Gloeidraad/ESP32-MUSIC-PLAYER/Hardware/V1/Doc/Images/ESP32-MUSIC-PLAYER-V1-BOT.png

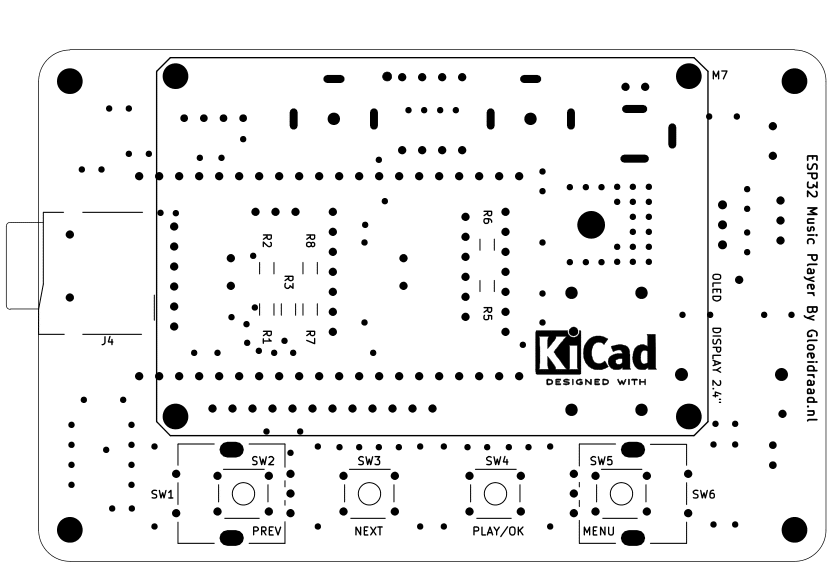
Hardware/V1/Doc/Images/ESP32-MUSIC-PLAYER-V1-BOT.png
