Gloeidraad/ESP32-MUSIC-PLAYER/Hardware/V1/Doc/Images/ESP32-MUSIC-PLAYER-V1-TOP.png

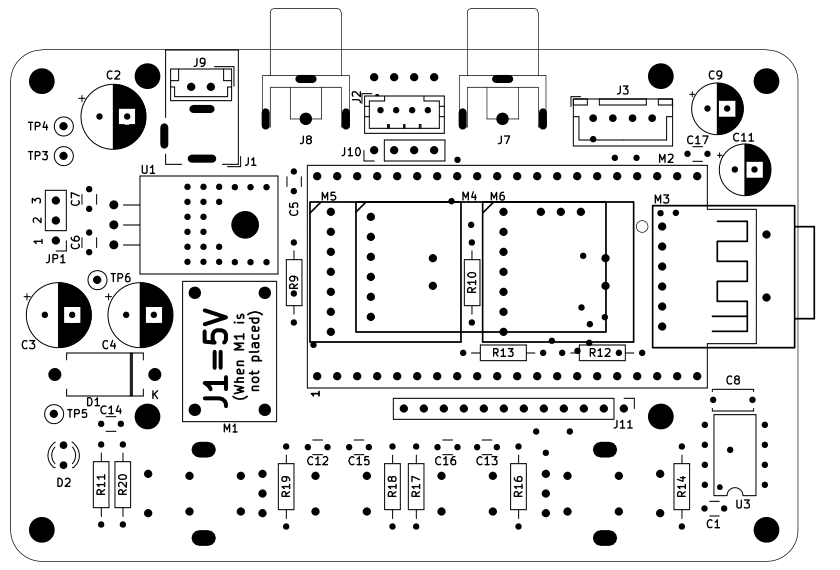
Hardware/V1/Doc/Images/ESP32-MUSIC-PLAYER-V1-TOP.png
