Gloeidraad/ESP32-MUSIC-PLAYER/Hardware/V5-SPI/ESP32-MUSIC-PLAYER-MINI-V5-PANEL/Images/assy side.png

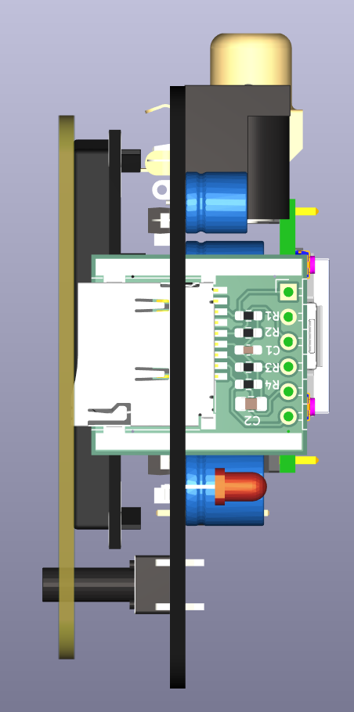
Hardware/V5-SPI/ESP32-MUSIC-PLAYER-MINI-V5-PANEL/Images/assy side.png
