Gloeidraad/ESP32-MUSIC-PLAYER/Hardware/V5-SPI/ESP32-MUSIC-PLAYER-MINI-V5-PANEL/Images/ESP23 Player in Strapubox 2515 front.jpg

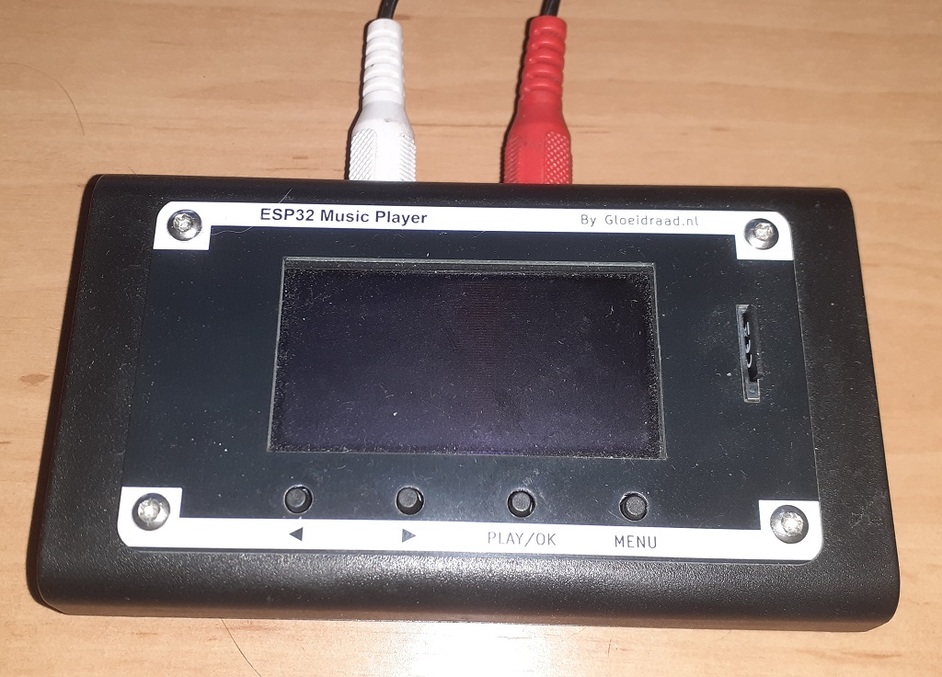
Hardware/V5-SPI/ESP32-MUSIC-PLAYER-MINI-V5-PANEL/Images/ESP23 Player in Strapubox 2515 front.jpg
