Gloeidraad/ESP32-MUSIC-PLAYER/Software/ESP32-Music-Player/src/AudioI2S/Audio.cpp

/*
 * Audio.cpp
 *
 *  Created on: Oct 26.2018
 *
 *  Version 3.0.10e
 *  Updated on: May 29.2024
 *      Author: Wolle (schreibfaul1)
 *
 */
#include "Audio.h"
#include "aac_decoder/aac_decoder.h"
#include "flac_decoder/flac_decoder.h"
#include "mp3_decoder/mp3_decoder.h"
#include "opus_decoder/opus_decoder.h"
#include "vorbis_decoder/vorbis_decoder.h"

//------------------------------------------------------------------------------------------------------------------------------------------------------------------------------------------------------
AudioBuffer::AudioBuffer(size_t maxBlockSize) {
    // if maxBlockSize isn't set use defaultspace (1600 bytes) is enough for aac and mp3 player
    if(maxBlockSize) m_resBuffSizeRAM = maxBlockSize;
    if(maxBlockSize) m_maxBlockSize = maxBlockSize;
}

AudioBuffer::~AudioBuffer() {
    if(m_buffer) free(m_buffer);
    m_buffer = NULL;
}

void AudioBuffer::setBufsize(int ram, int psram) {
    if(ram > -1) // -1 == default / no change
        m_buffSizeRAM = ram;
    if(psram > -1) m_buffSizePSRAM = psram;
}

int32_t AudioBuffer::getBufsize() { return m_buffSize; }

size_t AudioBuffer::init() {
    if(m_buffer) free(m_buffer);
    m_buffer = NULL;
    if(psramInit() && m_buffSizePSRAM > 0) {
        // PSRAM found, AudioBuffer will be allocated in PSRAM
        m_f_psram = true;
        m_buffSize = m_buffSizePSRAM;
        m_buffer = (uint8_t*)ps_calloc(m_buffSize, sizeof(uint8_t));
        m_buffSize = m_buffSizePSRAM - m_resBuffSizePSRAM;
    }
    if(m_buffer == NULL) {
        // PSRAM not found, not configured or not enough available
        m_f_psram = false;
        m_buffer = (uint8_t*)heap_caps_calloc(m_buffSizeRAM, sizeof(uint8_t), MALLOC_CAP_DEFAULT | MALLOC_CAP_INTERNAL);
        m_buffSize = m_buffSizeRAM - m_resBuffSizeRAM;
    }
    if(!m_buffer) return 0;
    m_f_init = true;
    resetBuffer();
    return m_buffSize;
}

void AudioBuffer::changeMaxBlockSize(uint16_t mbs) {
    m_maxBlockSize = mbs;
    return;
}

uint16_t AudioBuffer::getMaxBlockSize() { return m_maxBlockSize; }

size_t AudioBuffer::freeSpace() {
    if(m_readPtr >= m_writePtr) { m_freeSpace = (m_readPtr - m_writePtr); }
    else { m_freeSpace = (m_endPtr - m_writePtr) + (m_readPtr - m_buffer); }
    if(m_f_start) m_freeSpace = m_buffSize;
    return m_freeSpace - 1;
}

size_t AudioBuffer::writeSpace() {
    if(m_readPtr >= m_writePtr) {
        m_writeSpace = (m_readPtr - m_writePtr - 1); // readPtr must not be overtaken
    }
    else {
        if(getReadPos() == 0) m_writeSpace = (m_endPtr - m_writePtr - 1);
        else m_writeSpace = (m_endPtr - m_writePtr);
    }
    if(m_f_start) m_writeSpace = m_buffSize - 1;
    return m_writeSpace;
}

size_t AudioBuffer::bufferFilled() {
    if(m_writePtr >= m_readPtr) { m_dataLength = (m_writePtr - m_readPtr); }
    else { m_dataLength = (m_endPtr - m_readPtr) + (m_writePtr - m_buffer); }
    return m_dataLength;
}

size_t AudioBuffer::getMaxAvailableBytes() {
    if(m_writePtr >= m_readPtr) { m_dataLength = (m_writePtr - m_readPtr - 1); }
    else { m_dataLength = (m_endPtr - m_readPtr); }
    return m_dataLength;
}

void AudioBuffer::bytesWritten(size_t bw) {
    m_writePtr += bw;
    if(m_writePtr == m_endPtr) { m_writePtr = m_buffer; }
    if(bw && m_f_start) m_f_start = false;
}

void AudioBuffer::bytesWasRead(size_t br) {
    m_readPtr += br;
    if(m_readPtr >= m_endPtr) {
        size_t tmp = m_readPtr - m_endPtr;
        m_readPtr = m_buffer + tmp;
    }
}

uint8_t* AudioBuffer::getWritePtr() { return m_writePtr; }

uint8_t* AudioBuffer::getReadPtr() {
    size_t len = m_endPtr - m_readPtr;
    if(len < m_maxBlockSize) {                            // be sure the last frame is completed
        memcpy(m_endPtr, m_buffer, m_maxBlockSize - len); // cpy from m_buffer to m_endPtr with len
    }
    return m_readPtr;
}

void AudioBuffer::resetBuffer() {
    m_writePtr = m_buffer;
    m_readPtr = m_buffer;
    m_endPtr = m_buffer + m_buffSize;
    m_f_start = true;
    // memset(m_buffer, 0, m_buffSize); //Clear Inputbuffer
}

uint32_t AudioBuffer::getWritePos() { return m_writePtr - m_buffer; }

uint32_t AudioBuffer::getReadPos() { return m_readPtr - m_buffer; }
//------------------------------------------------------------------------------------------------------------------------------------------------------------------------------------------------------
// clang-format off
Audio::Audio(bool internalDAC /* = false */, uint8_t channelEnabled /* = I2S_SLOT_MODE_STEREO */, uint8_t i2sPort) {

    mutex_audio = xSemaphoreCreateMutex();

#ifdef AUDIO_LOG
    m_f_Log = true;
#endif

#define __malloc_heap_psram(size) \
    heap_caps_malloc_prefer(size, 2, MALLOC_CAP_DEFAULT | MALLOC_CAP_SPIRAM, MALLOC_CAP_DEFAULT | MALLOC_CAP_INTERNAL)

    m_f_psramFound = psramInit();
    if(m_f_psramFound) m_chbufSize = 4096; else m_chbufSize = 512 + 64;
    if(m_f_psramFound) m_ibuffSize = 4096; else m_ibuffSize = 512 + 64;
    m_lastHost = (char*)__malloc_heap_psram(512);
    m_outBuff = (int16_t*)__malloc_heap_psram(m_outbuffSize);
    m_chbuf = (char*)__malloc_heap_psram(m_chbufSize);
    m_ibuff = (char*)__malloc_heap_psram(m_ibuffSize);

    if(!m_chbuf || !m_lastHost || !m_outBuff || !m_ibuff) log_e("oom");

#define AUDIO_INFO(...)                     \
    {                                       \
        sprintf(m_ibuff, __VA_ARGS__);      \
        if(audio_info) audio_info(m_ibuff); \
    }

    clientsecure.setInsecure();
    m_f_channelEnabled = channelEnabled;
    m_f_internalDAC = internalDAC;
    m_i2s_num = i2sPort;  // i2s port number

    // -------- I2S configuration -------------------------------------------------------------------------------------------
#if ESP_IDF_VERSION_MAJOR == 5
    m_i2s_chan_cfg.id            = (i2s_port_t)m_i2s_num;  // I2S_NUM_AUTO, I2S_NUM_0, I2S_NUM_1
    m_i2s_chan_cfg.role          = I2S_ROLE_MASTER;        // I2S controller master role, bclk and lrc signal will be set to output
    m_i2s_chan_cfg.dma_desc_num  = 16;                     // number of DMA buffer
    m_i2s_chan_cfg.dma_frame_num = 512;                    // I2S frame number in one DMA buffer.
    m_i2s_chan_cfg.auto_clear    = true;                   // i2s will always send zero automatically if no data to send
    i2s_new_channel(&m_i2s_chan_cfg, &m_i2s_tx_handle, NULL);

    m_i2s_std_cfg.slot_cfg                = I2S_STD_PHILIPS_SLOT_DEFAULT_CONFIG(I2S_DATA_BIT_WIDTH_16BIT, I2S_SLOT_MODE_STEREO); // Set to enable bit shift in Philips mode
    m_i2s_std_cfg.gpio_cfg.bclk           = I2S_GPIO_UNUSED;           // BCLK, Assignment in setPinout()
    m_i2s_std_cfg.gpio_cfg.din            = I2S_GPIO_UNUSED;           // not used
    m_i2s_std_cfg.gpio_cfg.dout           = I2S_GPIO_UNUSED;           // DOUT, Assignment in setPinout()
    m_i2s_std_cfg.gpio_cfg.mclk           = I2S_GPIO_UNUSED;           // MCLK, Assignment in setPinout()
    m_i2s_std_cfg.gpio_cfg.ws             = I2S_GPIO_UNUSED;           // LRC,  Assignment in setPinout()
    m_i2s_std_cfg.gpio_cfg.invert_flags.mclk_inv = false;
    m_i2s_std_cfg.gpio_cfg.invert_flags.bclk_inv = false;
    m_i2s_std_cfg.gpio_cfg.invert_flags.ws_inv   = false;
    m_i2s_std_cfg.clk_cfg.sample_rate_hz = 44100;
    m_i2s_std_cfg.clk_cfg.clk_src        = I2S_CLK_SRC_DEFAULT;        // Select PLL_F160M as the default source clock
    m_i2s_std_cfg.clk_cfg.mclk_multiple  = I2S_MCLK_MULTIPLE_128;      // mclk = sample_rate * 256
    i2s_channel_init_std_mode(m_i2s_tx_handle, &m_i2s_std_cfg);
    I2Sstart(0);
    m_sampleRate = 44100;
#else
    m_i2s_config.sample_rate          = 16000;
    m_i2s_config.bits_per_sample      = I2S_BITS_PER_SAMPLE_16BIT;
    m_i2s_config.channel_format       = I2S_CHANNEL_FMT_RIGHT_LEFT;
    m_i2s_config.intr_alloc_flags     = ESP_INTR_FLAG_LEVEL1; // interrupt priority
    m_i2s_config.dma_buf_count        = 16;
    m_i2s_config.dma_buf_len          = 512;
    m_i2s_config.use_apll             = APLL_DISABLE; // must be disabled in V2.0.1-RC1
    m_i2s_config.tx_desc_auto_clear   = true;   // new in V1.0.1
    m_i2s_config.fixed_mclk           = true;
    m_i2s_config.mclk_multiple        = I2S_MCLK_MULTIPLE_128;

    if (internalDAC)  {
        #ifdef CONFIG_IDF_TARGET_ESP32  // ESP32S3 has no DAC
        printf("internal DAC");
        m_i2s_config.mode             = (i2s_mode_t)(I2S_MODE_MASTER | I2S_MODE_TX | I2S_MODE_DAC_BUILT_IN );
        m_i2s_config.communication_format = (i2s_comm_format_t)(I2S_COMM_FORMAT_STAND_MSB); // vers >= 2.0.5
        i2s_driver_install((i2s_port_t)m_i2s_num, &m_i2s_config, 0, NULL);
        i2s_set_dac_mode((i2s_dac_mode_t)m_f_channelEnabled);
        if(m_f_channelEnabled != I2S_DAC_CHANNEL_BOTH_EN) {
            m_f_forceMono = true;
        }
        #endif
    }
    else {
        m_i2s_config.mode             = (i2s_mode_t)(I2S_MODE_MASTER | I2S_MODE_TX);
        m_i2s_config.communication_format = (i2s_comm_format_t)(I2S_COMM_FORMAT_STAND_I2S); // Arduino vers. > 2.0.0
        i2s_driver_install((i2s_port_t)m_i2s_num, &m_i2s_config, 0, NULL);
        m_f_forceMono = false;
    }
    i2s_zero_dma_buffer((i2s_port_t) m_i2s_num);

#endif // ESP_IDF_VERSION_MAJOR == 5
    for(int i = 0; i < 3; i++) {
        m_filter[i].a0 = 1;
        m_filter[i].a1 = 0;
        m_filter[i].a2 = 0;
        m_filter[i].b1 = 0;
        m_filter[i].b2 = 0;
    }
    computeLimit();  // first init, vol = 21, vol_steps = 21
    m_headerTimeout = 2500; // OMT: expansion
}
//------------------------------------------------------------------------------------------------------------------------------------------------------------------------------------------------------
Audio::~Audio() {
    // I2Sstop(m_i2s_num);
    // InBuff.~AudioBuffer(); #215 the AudioBuffer is automatically destroyed by the destructor
    setDefaults();
    if(m_playlistBuff) {
        free(m_playlistBuff);
        m_playlistBuff = NULL;
    }
#if ESP_IDF_VERSION_MAJOR == 5
    i2s_del_channel(m_i2s_tx_handle);
#else
    i2s_driver_uninstall((i2s_port_t)m_i2s_num); // #215 free I2S buffer
#endif
    if(m_chbuf)       {free(m_chbuf);        m_chbuf        = NULL;}
    if(m_lastHost)    {free(m_lastHost);     m_lastHost     = NULL;}
    if(m_outBuff)     {free(m_outBuff);      m_outBuff      = NULL; }
    if(m_ibuff)       {free(m_ibuff);        m_ibuff        = NULL;}
    if(m_lastM3U8host){free(m_lastM3U8host); m_lastM3U8host = NULL;}

    vSemaphoreDelete(mutex_audio);
}
// clang-format on
//------------------------------------------------------------------------------------------------------------------------------------------------------------------------------------------------------
void Audio::setBufsize(int rambuf_sz, int psrambuf_sz) {
    if(InBuff.isInitialized()) {
        log_e("Audio::setBufsize must not be called after audio is initialized");
        return;
    }
    InBuff.setBufsize(rambuf_sz, psrambuf_sz);
};

void Audio::initInBuff() {
    if(!InBuff.isInitialized()) {
        size_t size = InBuff.init();
        if(size > 0) { AUDIO_INFO("PSRAM %sfound, inputBufferSize: %u bytes", InBuff.havePSRAM() ? "" : "not ", size - 1); }
    }
    changeMaxBlockSize(1600); // default size mp3 or aac
}

//------------------------------------------------------------------------------------------------------------------------------------------------------------------------------------------------------
esp_err_t Audio::I2Sstart(uint8_t i2s_num) {
#if ESP_IDF_VERSION_MAJOR == 5
    return i2s_channel_enable(m_i2s_tx_handle);
#else
    // It is not necessary to call this function after i2s_driver_install() (it is started automatically),
    // however it is necessary to call it after i2s_stop()
    return i2s_start((i2s_port_t)i2s_num);
#endif
}

esp_err_t Audio::I2Sstop(uint8_t i2s_num) {
#if ESP_IDF_VERSION_MAJOR == 5
    return i2s_channel_disable(m_i2s_tx_handle);
#else
    return i2s_stop((i2s_port_t)i2s_num);
#endif
}
//------------------------------------------------------------------------------------------------------------------------------------------------------------------------------------------------------
void Audio::setDefaults() {
    stopSong();
    initInBuff(); // initialize InputBuffer if not already done
    InBuff.resetBuffer();
    MP3Decoder_FreeBuffers();
    FLACDecoder_FreeBuffers();
    AACDecoder_FreeBuffers();
    OPUSDecoder_FreeBuffers();
    VORBISDecoder_FreeBuffers();
    if(m_playlistBuff) {
        free(m_playlistBuff);
        m_playlistBuff = NULL;
    } // free if stream is not m3u8
    vector_clear_and_shrink(m_playlistURL);
    vector_clear_and_shrink(m_playlistContent);
    m_hashQueue.clear();
    m_hashQueue.shrink_to_fit(); // uint32_t vector
    client.stop();
    clientsecure.stop();
    _client = static_cast<WiFiClient*>(&client); /* default to *something* so that no NULL deref can happen */
    ts_parsePacket(0, 0, 0);                     // reset ts routine
    if(m_lastM3U8host) {
        free(m_lastM3U8host);
        m_lastM3U8host = NULL;
    }
    AUDIO_INFO("buffers freed, free Heap: %lu bytes", (long unsigned int)ESP.getFreeHeap());

    m_f_timeout = false;
    m_f_chunked = false; // Assume not chunked
    m_f_firstmetabyte = false;
    m_f_playing = false;
    m_f_ssl = false;
    m_f_metadata = false;
    m_f_tts = false;
    m_f_firstCall = true;        // InitSequence for processWebstream and processLocalFile
    m_f_firstCurTimeCall = true; // InitSequence for computeAudioTime
    m_f_firstM3U8call = true;    // InitSequence for parsePlaylist_M3U8
    m_f_running = false;
    m_f_loop = false;     // Set if audio file should loop
    m_f_unsync = false;   // set within ID3 tag but not used
    m_f_exthdr = false;   // ID3 extended header
    m_f_rtsp = false;     // RTSP (m3u8)stream
    m_f_m3u8data = false; // set again in processM3U8entries() if necessary
    m_f_continue = false;
    m_f_ts = false;
    m_f_m4aID3dataAreRead = false;

    m_streamType = ST_NONE;
    m_codec = CODEC_NONE;
    m_playlistFormat = FORMAT_NONE;
    m_datamode = AUDIO_NONE;
    m_audioCurrentTime = 0; // Reset playtimer
    m_audioFileDuration = 0;
    m_audioDataStart = 0;
    m_audioDataSize = 0;
    m_avr_bitrate = 0;     // the same as m_bitrate if CBR, median if VBR
    m_bitRate = 0;         // Bitrate still unknown
    m_bytesNotDecoded = 0; // counts all not decodable bytes
    m_chunkcount = 0;      // for chunked streams
   // byteCounter = 0;     // count received data
    m_contentlength = 0;   // If Content-Length is known, count it
    m_curSample = 0;
    m_metaint = 0;        // No metaint yet
    m_LFcount = 0;        // For end of header detection
    m_controlCounter = 0; // Status within readID3data() and readWaveHeader()
    m_channels = 2;       // assume stereo #209
    m_streamTitleHash = 0;
    m_fileSize = 0;
    m_ID3Size = 0;
    m_haveNewFilePos = 0;
}

//------------------------------------------------------------------------------------------------------------------------------------------------------------------------------------------------------
void Audio::setConnectionTimeout(uint16_t timeout_ms, uint16_t timeout_ms_ssl) {
    if(timeout_ms) m_timeout_ms = timeout_ms;
    if(timeout_ms_ssl) m_timeout_ms_ssl = timeout_ms_ssl;
}

/*
    Text to speech API provides a speech endpoint based on our TTS (text-to-speech) model.
    More info: https://platform.openai.com/docs/guides/text-to-speech/text-to-speech

    Request body:
    model (string) [Required] - One of the available TTS models: tts-1 or tts-1-hd
    input (string) [Required] - The text to generate audio for. The maximum length is 4096 characters.
    voice (string) [Required] - The voice to use when generating the audio. Supported voices are alloy, echo, fable, onyx, nova, and shimmer.
    response_format (string) [Optional] - Defaults to mp3. The format to audio in. Supported formats are mp3, opus, aac, and flac.
    speed (number) [Optional] - Defaults to 1. The speed of the generated audio. Select a value from 0.25 to 4.0. 1.0 is the default.

    Usage: audio.openai_speech(OPENAI_API_KEY, "tts-1", input, "shimmer", "mp3", "1");
*/
bool Audio::openai_speech(const String& api_key, const String& model, const String& input, const String& voice, const String& response_format, const String& speed) {
    char host[] = "api.openai.com";
    char path[] = "/v1/audio/speech";

    xSemaphoreTakeRecursive(mutex_audio, portMAX_DELAY);

    if (input == "") {
        AUDIO_INFO("input text is empty");
        stopSong();
        xSemaphoreGiveRecursive(mutex_audio);
        return false;
    }

    AUDIO_INFO("Connect to new host: \"%s\"", host);
    setDefaults();
    m_f_ssl = true;

    String input_clean = "";
    for (int i = 0; i < input.length(); i++) {
        char c = input.charAt(i);
        if (c == '\"') {
            input_clean += "\\\"";
        } else if (c == '\n') {
            input_clean += "\\n";
        } else {
            input_clean += c;
        }
    }

    String post_body = "{"
        "\"model\": \"" + model + "\"," +
        "\"input\": \"" + input_clean + "\"," +
        "\"voice\": \"" + voice + "\"," +
        "\"response_format\": \"" + response_format + "\"," +
        "\"speed\": \"" + speed + "\"" +
    "}";

    String http_request =
        "POST " + String(path) + " HTTP/1.0\r\n" // UNKNOWN ERROR CODE (0050) - crashing on HTTP/1.1 need to use HTTP/1.0
        + "Host: " + String(host) + "\r\n"
        + "Authorization: Bearer " + api_key + "\r\n"
        + "Accept-Encoding: identity;q=1,*;q=0\r\n"
        + "User-Agent: nArija/1.0\r\n"
        + "Content-Type: application/json; charset=utf-8\r\n"
        + "Content-Length: " + post_body.length() + "\r\n"
        + "Connection: keep-alive\r\n" + "\r\n"
        + post_body + "\r\n"
    ;

    bool res = true;
    int port = 443;
    _client = static_cast<WiFiClient*>(&clientsecure);

    uint32_t t = millis();
    if (m_f_Log) AUDIO_INFO("connect to %s on port %d path %s", host, port, path);
    res = _client->connect(host, port, m_timeout_ms_ssl);
    if (res) {
        uint32_t dt = millis() - t;
        strcpy(m_lastHost, host);
        AUDIO_INFO("%s has been established in %lu ms, free Heap: %lu bytes", "SSL", (long unsigned int) dt, (long unsigned int) ESP.getFreeHeap());
        m_f_running = true;
    }

    m_expectedCodec = CODEC_NONE;
    m_expectedPlsFmt = FORMAT_NONE;

    if (res) {
        _client->print(http_request);
        if (response_format == "mp3") m_expectedCodec  = CODEC_MP3;
        if (response_format == "opus") m_expectedCodec  = CODEC_OPUS;
        if (response_format == "aac") m_expectedCodec  = CODEC_AAC;
        if (response_format == "flac") m_expectedCodec  = CODEC_FLAC;
        setDatamode(HTTP_RESPONSE_HEADER);
        m_streamType = ST_WEBSTREAM;
    } else {
        AUDIO_INFO("Request %s failed!", host);
        m_lastHost[0] = 0;
    }

    xSemaphoreGiveRecursive(mutex_audio);
    return res;
}

//------------------------------------------------------------------------------------------------------------------------------------------------------------------------------------------------------
bool Audio::connecttohost(const char* host, const char* user, const char* pwd) {
    // user and pwd for authentification only, can be empty

    xSemaphoreTakeRecursive(mutex_audio, portMAX_DELAY);

    if(host == NULL) {
        AUDIO_INFO("Hostaddress is empty");
        stopSong();
        xSemaphoreGiveRecursive(mutex_audio);
        return false;
    }

    uint16_t lenHost = strlen(host);

    if(lenHost >= 512 - 10) {
        AUDIO_INFO("Hostaddress is too long");
        stopSong();
        xSemaphoreGiveRecursive(mutex_audio);
        return false;
    }

    int   idx = indexOf(host, "http");
    char* l_host = (char*)malloc(lenHost + 10);
    if(idx < 0) {
        strcpy(l_host, "http://");
        strcat(l_host, host);
    }                                      // amend "http;//" if not found
    else { strcpy(l_host, (host + idx)); } // trim left if necessary

    char* h_host = NULL; // pointer of l_host without http:// or https://
    if(startsWith(l_host, "https")) h_host = strdup(l_host + 8);
    else h_host = strdup(l_host + 7);

    // initializationsequence
    int16_t  pos_slash;     // position of "/" in hostname
    int16_t  pos_colon;     // position of ":" in hostname
    int16_t  pos_ampersand; // position of "&" in hostname
    uint16_t port = 80;     // port number

    // In the URL there may be an extension, like noisefm.ru:8000/play.m3u&t=.m3u
    pos_slash = indexOf(h_host, "/", 0);
    pos_colon = indexOf(h_host, ":", 0);
    if(isalpha(h_host[pos_colon + 1])) pos_colon = -1; // no portnumber follows
    pos_ampersand = indexOf(h_host, "&", 0);

    char* hostwoext = NULL; // "skonto.ls.lv:8002" in "skonto.ls.lv:8002/mp3"
    char* extension = NULL; // "/mp3" in "skonto.ls.lv:8002/mp3"

    if(pos_slash > 1) {
        hostwoext = (char*)malloc(pos_slash + 1);
        memcpy(hostwoext, h_host, pos_slash);
        hostwoext[pos_slash] = '\0';
        uint16_t extLen = urlencode_expected_len(h_host + pos_slash);
        extension = (char*)malloc(extLen + 20);
        memcpy(extension, h_host + pos_slash, extLen);
        urlencode(extension, extLen, true);
    }
    else { // url has no extension
        hostwoext = strdup(h_host);
        extension = strdup("/");
    }

    if((pos_colon >= 0) && ((pos_ampersand == -1) || (pos_ampersand > pos_colon))) {
        port = atoi(h_host + pos_colon + 1); // Get portnumber as integer
        hostwoext[pos_colon] = '\0';         // Host without portnumber
    }

    AUDIO_INFO("Connect to new host: \"%s\"", l_host);
    setDefaults(); // no need to stop clients if connection is established (default is true)

    if(startsWith(l_host, "https")) m_f_ssl = true;
    else m_f_ssl = false;

    // optional basic authorization
    uint16_t auth = strlen(user) + strlen(pwd);
    char     authorization[base64_encode_expected_len(auth + 1) + 1];
    authorization[0] = '\0';
    if(auth > 0) {
        char toEncode[auth + 4];
        strcpy(toEncode, user);
        strcat(toEncode, ":");
        strcat(toEncode, pwd);
        b64encode((const char*)toEncode, strlen(toEncode), authorization);
    }

    //  AUDIO_INFO("Connect to \"%s\" on port %d, extension \"%s\"", hostwoext, port, extension);

    char rqh[strlen(h_host) + strlen(authorization) + 220]; // http request header
    rqh[0] = '\0';

    strcat(rqh, "GET ");
    strcat(rqh, extension);
    strcat(rqh, " HTTP/1.1\r\n");
    strcat(rqh, "Host: ");
    strcat(rqh, hostwoext);
    strcat(rqh, "\r\n");
    strcat(rqh, "Icy-MetaData:1\r\n");
    strcat(rqh, "Icy-MetaData:2\r\n");

    if(auth > 0) {
        strcat(rqh, "Authorization: Basic ");
        strcat(rqh, authorization);
        strcat(rqh, "\r\n");
    }

    strcat(rqh, "Accept-Encoding: identity;q=1,*;q=0\r\n");
    //    strcat(rqh, "User-Agent: Mozilla/5.0\r\n"); #363
    strcat(rqh, "Connection: keep-alive\r\n\r\n");

    //    if(ESP_ARDUINO_VERSION_MAJOR == 2 && ESP_ARDUINO_VERSION_MINOR == 0 && ESP_ARDUINO_VERSION_PATCH >= 3){
    //        m_timeout_ms_ssl = UINT16_MAX;  // bug in v2.0.3 if hostwoext is a IPaddr not a name
    //        m_timeout_ms = UINT16_MAX;  // [WiFiClient.cpp:253] connect(): select returned due to timeout 250 ms for
    //        fd 48
    //    } fix in V2.0.8

    bool res = true; // no need to reconnect if connection exists

    if(m_f_ssl) {
        _client = static_cast<WiFiClient*>(&clientsecure);
        if(port == 80) port = 443;
    }
    else { _client = static_cast<WiFiClient*>(&client); }

    uint32_t t = millis();
    if(m_f_Log) AUDIO_INFO("connect to %s on port %d path %s", hostwoext, port, extension);
    res = _client->connect(hostwoext, port, m_f_ssl ? m_timeout_ms_ssl : m_timeout_ms);
    if(res) {
        uint32_t dt = millis() - t;
        strcpy(m_lastHost, l_host);
        AUDIO_INFO("%s has been established in %lu ms, free Heap: %lu bytes", m_f_ssl ? "SSL" : "Connection", (long unsigned int)dt, (long unsigned int)ESP.getFreeHeap());
        m_f_running = true;
    }

    m_expectedCodec = CODEC_NONE;
    m_expectedPlsFmt = FORMAT_NONE;

    if(res) {
    //    log_i("connecttohost(): %s", rqh);
        _client->print(rqh);
        if(endsWith(extension, ".mp3" )) m_expectedCodec  = CODEC_MP3;
        if(endsWith(extension, ".aac" )) m_expectedCodec  = CODEC_AAC;
        if(endsWith(extension, ".wav" )) m_expectedCodec  = CODEC_WAV;
        if(endsWith(extension, ".m4a" )) m_expectedCodec  = CODEC_M4A;
        if(endsWith(extension, ".ogg" )) m_expectedCodec  = CODEC_OGG;
        if(endsWith(extension, ".flac")) m_expectedCodec  = CODEC_FLAC;
        if(endsWith(extension, "-flac")) m_expectedCodec  = CODEC_FLAC;
        if(endsWith(extension, ".opus")) m_expectedCodec  = CODEC_OPUS;
        if(endsWith(extension, "/opus")) m_expectedCodec  = CODEC_OPUS;
        if(endsWith(extension, ".asx" )) m_expectedPlsFmt = FORMAT_ASX;
        if(endsWith(extension, ".m3u" )) m_expectedPlsFmt = FORMAT_M3U;
        if(endsWith(extension, ".pls" )) m_expectedPlsFmt = FORMAT_PLS;
        if(endsWith(extension, ".m3u8")) {
            m_expectedPlsFmt = FORMAT_M3U8;
            if(audio_lasthost) audio_lasthost(host);
        }
        setDatamode(HTTP_RESPONSE_HEADER); // Handle header
        m_streamType = ST_WEBSTREAM;
    }
    else {
        AUDIO_INFO("Request %s failed!", l_host);
        if(audio_showstation) audio_showstation("");
        if(audio_showstreamtitle) audio_showstreamtitle("");
        if(audio_icydescription) audio_icydescription("");
        if(audio_icyurl) audio_icyurl("");
        m_lastHost[0] = 0;
    }
    if(hostwoext) {
        free(hostwoext);
        hostwoext = NULL;
    }
    if(extension) {
        free(extension);
        extension = NULL;
    }
    if(l_host) {
        free(l_host);
        l_host = NULL;
    }
    if(h_host) {
        free(h_host);
        h_host = NULL;
    }
    xSemaphoreGiveRecursive(mutex_audio);
    return res;
}
//------------------------------------------------------------------------------------------------------------------------------------------------------------------------------------------------------
bool Audio::httpPrint(const char* host) {
    // user and pwd for authentification only, can be empty

    if(host == NULL) {
        AUDIO_INFO("Hostaddress is empty");
        stopSong();
        return false;
    }

    char* h_host = NULL; // pointer of l_host without http:// or https://

    if(startsWith(host, "https")) m_f_ssl = true;
    else m_f_ssl = false;

    if(m_f_ssl) h_host = strdup(host + 8);
    else h_host = strdup(host + 7);

    int16_t  pos_slash;     // position of "/" in hostname
    int16_t  pos_colon;     // position of ":" in hostname
    int16_t  pos_ampersand; // position of "&" in hostname
    uint16_t port = 80;     // port number

    // In the URL there may be an extension, like noisefm.ru:8000/play.m3u&t=.m3u
    pos_slash = indexOf(h_host, "/", 0);
    pos_colon = indexOf(h_host, ":", 0);
    if(isalpha(h_host[pos_colon + 1])) pos_colon = -1; // no portnumber follows
    pos_ampersand = indexOf(h_host, "&", 0);

    char* hostwoext = NULL; // "skonto.ls.lv:8002" in "skonto.ls.lv:8002/mp3"
    char* extension = NULL; // "/mp3" in "skonto.ls.lv:8002/mp3"

    if(pos_slash > 1) {
        hostwoext = (char*)malloc(pos_slash + 1);
        memcpy(hostwoext, h_host, pos_slash);
        hostwoext[pos_slash] = '\0';
        uint16_t extLen = urlencode_expected_len(h_host + pos_slash);
        extension = (char*)malloc(extLen + 20);
        memcpy(extension, h_host + pos_slash, extLen);
        urlencode(extension, extLen, true);
    }
    else { // url has no extension
        hostwoext = strdup(h_host);
        extension = strdup("/");
    }

    if((pos_colon >= 0) && ((pos_ampersand == -1) || (pos_ampersand > pos_colon))) {
        port = atoi(h_host + pos_colon + 1); // Get portnumber as integer
        hostwoext[pos_colon] = '\0';         // Host without portnumber
    }

    AUDIO_INFO("new request: \"%s\"", host);

    char rqh[strlen(h_host) + 200]; // http request header
    rqh[0] = '\0';

    strcat(rqh, "GET ");
    strcat(rqh, extension);
    strcat(rqh, " HTTP/1.1\r\n");
    strcat(rqh, "Host: ");
    strcat(rqh, hostwoext);
    strcat(rqh, "\r\n");
    strcat(rqh, "Accept-Encoding: identity;q=1,*;q=0\r\n");
    //    strcat(rqh, "User-Agent: Mozilla/5.0\r\n"); #363
    strcat(rqh, "Connection: keep-alive\r\n\r\n");

    if(m_f_ssl) {
        _client = static_cast<WiFiClient*>(&clientsecure);
        if(port == 80) port = 443;
    }
    else { _client = static_cast<WiFiClient*>(&client); }
    if(!_client->connected()) {
        AUDIO_INFO("The host has disconnected, reconnecting");
        if(!_client->connect(hostwoext, port)) {
            log_e("connection lost");
            stopSong();
            return false;
        }
    }
    _client->print(rqh);
    if(endsWith(extension, ".mp3"))       m_expectedCodec  = CODEC_MP3;
    if(endsWith(extension, ".aac"))       m_expectedCodec  = CODEC_AAC;
    if(endsWith(extension, ".wav"))       m_expectedCodec  = CODEC_WAV;
    if(endsWith(extension, ".m4a"))       m_expectedCodec  = CODEC_M4A;
    if(endsWith(extension, ".flac"))      m_expectedCodec  = CODEC_FLAC;
    if(endsWith(extension, ".asx"))       m_expectedPlsFmt = FORMAT_ASX;
    if(endsWith(extension, ".m3u"))       m_expectedPlsFmt = FORMAT_M3U;
    if(indexOf( extension, ".m3u8") >= 0) m_expectedPlsFmt = FORMAT_M3U8;
    if(endsWith(extension, ".pls"))       m_expectedPlsFmt = FORMAT_PLS;

    setDatamode(HTTP_RESPONSE_HEADER); // Handle header
    m_streamType = ST_WEBSTREAM;
    m_contentlength = 0;
    m_f_chunked = false;

    if(hostwoext) {
        free(hostwoext);
        hostwoext = NULL;
    }
    if(extension) {
        free(extension);
        extension = NULL;
    }
    if(h_host) {
        free(h_host);
        h_host = NULL;
    }
    return true;
}
//------------------------------------------------------------------------------------------------------------------------------------------------------------------------------------------------------
bool Audio::setFileLoop(bool input) {
    if(m_codec == CODEC_M4A) return 0;
    m_f_loop = input;
    return input;
}
//------------------------------------------------------------------------------------------------------------------------------------------------------------------------------------------------------
// clang-format off
void Audio::UTF8toASCII(char* str) {

    const uint8_t ascii[60] = {
    //129, 130, 131, 132, 133, 134, 135, 136, 137, 138, 139, 140, 141, 142, 143, 144, 145, 146, 147, 148  // UTF8(C3)
    //                Ä    Å    Æ    Ç         É                                       Ñ                  // CHAR
      000, 000, 000, 142, 143, 146, 128, 000, 144, 000, 000, 000, 000, 000, 000, 000, 165, 000, 000, 000, // ASCII
    //149, 150, 151, 152, 153, 154, 155, 156, 157, 158, 159, 160, 161, 162, 163, 164, 165, 166, 167, 168
    //      Ö                             Ü              ß    à                   ä    å    æ         è
      000, 153, 000, 000, 000, 000, 000, 154, 000, 000, 225, 133, 000, 000, 000, 132, 134, 145, 000, 138,
    //169, 170, 171, 172. 173. 174. 175, 176, 177, 179, 179, 180, 181, 182, 183, 184, 185, 186, 187, 188
    //      ê    ë    ì         î    ï         ñ    ò         ô         ö              ù         û    ü
      000, 136, 137, 141, 000, 140, 139, 000, 164, 149, 000, 147, 000, 148, 000, 000, 151, 000, 150, 129};

    uint16_t i = 0, j = 0, s = 0;
    bool     f_C3_seen = false;

    while(str[i] != 0) {    // convert UTF8 to ASCII
        if(str[i] == 195) { // C3
            i++;
            f_C3_seen = true;
            continue;
        }
        str[j] = str[i];
        if(str[j] > 128 && str[j] < 189 && f_C3_seen == true) {
            s = ascii[str[j] - 129];
            if(s != 0) str[j] = s; // found a related ASCII sign
            f_C3_seen = false;
        }
        i++;
        j++;
    }
    str[j] = 0;
}
// clang-format on
//------------------------------------------------------------------------------------------------------------------------------------------------------------------------------------------------------
bool Audio::connecttoFS(fs::FS& fs, const char* path, int32_t fileStartPos) {

    if(!path) { // guard
        printProcessLog(AUDIOLOG_PATH_IS_NULL);
        return false;
    }

    xSemaphoreTakeRecursive(mutex_audio, portMAX_DELAY); // #3

    m_fileStartPos = fileStartPos;
    setDefaults(); // free buffers an set defaults

    char *audioPath = (char *) __malloc_heap_psram(strlen(path) + 2);
    if(!audioPath){
        printProcessLog(AUDIOLOG_OUT_OF_MEMORY);
        xSemaphoreGiveRecursive(mutex_audio);
        return false;
    }
    if(path[0] == '/'){strcpy(audioPath, path);}
    else {audioPath[0] = '/'; strcpy(audioPath + 1, path);}

    if(!fs.exists(audioPath)) {
        UTF8toASCII(audioPath);
        if(!fs.exists(audioPath)){
            printProcessLog(AUDIOLOG_FILE_NOT_FOUND, audioPath);
            xSemaphoreGiveRecursive(mutex_audio);
            free(audioPath);
            return false;
        }
    }

    AUDIO_INFO("Reading file: \"%s\"", audioPath);
    audiofile = fs.open(audioPath);

    if(!audiofile) {
        printProcessLog(AUDIOLOG_FILE_READ_ERR, audioPath);
        free(audioPath);
        xSemaphoreGiveRecursive(mutex_audio);
        return false;
    }

    setDatamode(AUDIO_LOCALFILE);
    m_fileSize = audiofile.size(); // TEST loop

    char* afn = NULL; // audioFileName
    afn = strdup(audiofile.name());

    uint8_t dotPos = lastIndexOf(afn, ".");
    for(uint8_t i = dotPos + 1; i < strlen(afn); i++) { afn[i] = toLowerCase(afn[i]); }

    if(endsWith(afn, ".mp3")) m_codec = CODEC_MP3; // m_codec is by default CODEC_NONE
    if(endsWith(afn, ".m4a")) m_codec = CODEC_M4A;
    if(endsWith(afn, ".aac")) m_codec = CODEC_AAC;
    if(endsWith(afn, ".wav")) m_codec = CODEC_WAV;
    if(endsWith(afn, ".flac")) m_codec = CODEC_FLAC;
    if(endsWith(afn, ".opus")) m_codec = CODEC_OPUS;
    if(endsWith(afn, ".ogg")) m_codec = CODEC_OGG;
    if(endsWith(afn, ".oga")) m_codec = CODEC_OGG;

    if(m_codec == CODEC_NONE) AUDIO_INFO("The %s format is not supported", afn + dotPos);

    if(afn) {
        free(afn);
        afn = NULL;
    }
    free(audioPath);

    bool ret = initializeDecoder();
    if(ret) m_f_running = true;
    else audiofile.close();
    xSemaphoreGiveRecursive(mutex_audio);
    return ret;
}
//------------------------------------------------------------------------------------------------------------------------------------------------------------------------------------------------------
bool Audio::connecttospeech(const char* speech, const char* lang) {
    xSemaphoreTakeRecursive(mutex_audio, portMAX_DELAY);

    setDefaults();
    char host[] = "translate.google.com.vn";
    char path[] = "/translate_tts";

    uint16_t speechLen = strlen(speech);
    uint16_t speechBuffLen = speechLen + 300;
    memcpy(m_lastHost, speech, 256);
    char* speechBuff = (char*)malloc(speechBuffLen);
    if(!speechBuff) {
        log_e("out of memory");
        xSemaphoreGiveRecursive(mutex_audio);
        return false;
    }
    memcpy(speechBuff, speech, speechLen);
    speechBuff[speechLen] = '\0';
    urlencode(speechBuff, speechBuffLen);

    char resp[strlen(speechBuff) + 200] = "";
    strcat(resp, "GET ");
    strcat(resp, path);
    strcat(resp, "?ie=UTF-8&tl=");
    strcat(resp, lang);
    strcat(resp, "&client=tw-ob&q=");
    strcat(resp, speechBuff);
    strcat(resp, " HTTP/1.1\r\n");
    strcat(resp, "Host: ");
    strcat(resp, host);
    strcat(resp, "\r\n");
    strcat(resp, "User-Agent: Mozilla/5.0 \r\n");
    strcat(resp, "Accept-Encoding: identity\r\n");
    strcat(resp, "Accept: text/html\r\n");
    strcat(resp, "Connection: close\r\n\r\n");

    if(speechBuff) {
        free(speechBuff);
        speechBuff = NULL;
    }
    _client = static_cast<WiFiClient*>(&client);
    if(!_client->connect(host, 80)) {
        log_e("Connection failed");
        xSemaphoreGiveRecursive(mutex_audio);
        return false;
    }
    _client->print(resp);

    m_streamType = ST_WEBFILE;
    m_f_running = true;
    m_f_ssl = false;
    m_f_tts = true;
    setDatamode(HTTP_RESPONSE_HEADER);
    xSemaphoreGiveRecursive(mutex_audio);
    return true;
}
//------------------------------------------------------------------------------------------------------------------------------------------------------------------------------------------------------
void Audio::urlencode(char* buff, uint16_t buffLen, bool spacesOnly) {
    uint16_t len = strlen(buff);
    uint8_t* tmpbuff = (uint8_t*)malloc(buffLen);
    if(!tmpbuff) {
        log_e("out of memory");
        return;
    }
    char     c;
    char     code0;
    char     code1;
    uint16_t j = 0;
    for(int i = 0; i < len; i++) {
        c = buff[i];
        if(isalnum(c)) tmpbuff[j++] = c;
        else if(spacesOnly) {
            if(c == ' ') {
                tmpbuff[j++] = '%';
                tmpbuff[j++] = '2';
                tmpbuff[j++] = '0';
            }
            else { tmpbuff[j++] = c; }
        }
        else {
            code1 = (c & 0xf) + '0';
            if((c & 0xf) > 9) code1 = (c & 0xf) - 10 + 'A';
            c = (c >> 4) & 0xf;
            code0 = c + '0';
            if(c > 9) code0 = c - 10 + 'A';
            tmpbuff[j++] = '%';
            tmpbuff[j++] = code0;
            tmpbuff[j++] = code1;
        }
        if(j == buffLen - 1) {
            log_e("out of memory");
            break;
        }
    }
    memcpy(buff, tmpbuff, j);
    buff[j] = '\0';
    free(tmpbuff);
}
//------------------------------------------------------------------------------------------------------------------------------------------------------------------------------------------------------
void Audio::showID3Tag(const char* tag, const char* value) {
    m_chbuf[0] = 0;
    // V2.2
    if(!strcmp(tag, "CNT")) sprintf(m_chbuf, "Play counter: %s", value);
    // if(!strcmp(tag, "COM")) sprintf(m_chbuf, "Comments: %s", value);
    if(!strcmp(tag, "CRA")) sprintf(m_chbuf, "Audio encryption: %s", value);
    if(!strcmp(tag, "CRM")) sprintf(m_chbuf, "Encrypted meta frame: %s", value);
    if(!strcmp(tag, "ETC")) sprintf(m_chbuf, "Event timing codes: %s", value);
    if(!strcmp(tag, "EQU")) sprintf(m_chbuf, "Equalization: %s", value);
    if(!strcmp(tag, "IPL")) sprintf(m_chbuf, "Involved people list: %s", value);
    if(!strcmp(tag, "PIC")) sprintf(m_chbuf, "Attached picture: %s", value);
    if(!strcmp(tag, "SLT")) sprintf(m_chbuf, "Synchronized lyric/text: %s", value);
    if(!strcmp(tag, "TAL")) sprintf(m_chbuf, "Album/Movie/Show title: %s", value);
    if(!strcmp(tag, "TBP")) sprintf(m_chbuf, "BPM (Beats Per Minute): %s", value);
    if(!strcmp(tag, "TCM")) sprintf(m_chbuf, "Composer: %s", value);
    if(!strcmp(tag, "TCO")) sprintf(m_chbuf, "Content type: %s", value);
    if(!strcmp(tag, "TCR")) sprintf(m_chbuf, "Copyright message: %s", value);
    if(!strcmp(tag, "TDA")) sprintf(m_chbuf, "Date: %s", value);
    if(!strcmp(tag, "TDY")) sprintf(m_chbuf, "Playlist delay: %s", value);
    if(!strcmp(tag, "TEN")) sprintf(m_chbuf, "Encoded by: %s", value);
    if(!strcmp(tag, "TFT")) sprintf(m_chbuf, "File type: %s", value);
    if(!strcmp(tag, "TIM")) sprintf(m_chbuf, "Time: %s", value);
    if(!strcmp(tag, "TKE")) sprintf(m_chbuf, "Initial key: %s", value);
    if(!strcmp(tag, "TLA")) sprintf(m_chbuf, "Language(s): %s", value);
    if(!strcmp(tag, "TLE")) sprintf(m_chbuf, "Length: %s", value);
    if(!strcmp(tag, "TMT")) sprintf(m_chbuf, "Media type: %s", value);
    if(!strcmp(tag, "TOA")) sprintf(m_chbuf, "Original artist(s)/performer(s): %s", value);
    if(!strcmp(tag, "TOF")) sprintf(m_chbuf, "Original filename: %s", value);
    if(!strcmp(tag, "TOL")) sprintf(m_chbuf, "Original Lyricist(s)/text writer(s): %s", value);
    if(!strcmp(tag, "TOR")) sprintf(m_chbuf, "Original release year: %s", value);
    if(!strcmp(tag, "TOT")) sprintf(m_chbuf, "Original album/Movie/Show title: %s", value);
    if(!strcmp(tag, "TP1")) sprintf(m_chbuf, "Lead artist(s)/Lead performer(s)/Soloist(s)/Performing group: %s", value);
    if(!strcmp(tag, "TP2")) sprintf(m_chbuf, "Band/Orchestra/Accompaniment: %s", value);
    if(!strcmp(tag, "TP3")) sprintf(m_chbuf, "Conductor/Performer refinement: %s", value);
    if(!strcmp(tag, "TP4")) sprintf(m_chbuf, "Interpreted, remixed, or otherwise modified by: %s", value);
    if(!strcmp(tag, "TPA")) sprintf(m_chbuf, "Part of a set: %s", value);
    if(!strcmp(tag, "TPB")) sprintf(m_chbuf, "Publisher: %s", value);
    if(!strcmp(tag, "TRC")) sprintf(m_chbuf, "ISRC (International Standard Recording Code): %s", value);
    if(!strcmp(tag, "TRD")) sprintf(m_chbuf, "Recording dates: %s", value);
    if(!strcmp(tag, "TRK")) sprintf(m_chbuf, "Track number/Position in set: %s", value);
    if(!strcmp(tag, "TSI")) sprintf(m_chbuf, "Size: %s", value);
    if(!strcmp(tag, "TSS")) sprintf(m_chbuf, "Software/hardware and settings used for encoding: %s", value);
    if(!strcmp(tag, "TT1")) sprintf(m_chbuf, "Content group description: %s", value);
    if(!strcmp(tag, "TT2")) sprintf(m_chbuf, "Title/Songname/Content description: %s", value);
    if(!strcmp(tag, "TT3")) sprintf(m_chbuf, "Subtitle/Description refinement: %s", value);
    if(!strcmp(tag, "TXT")) sprintf(m_chbuf, "Lyricist/text writer: %s", value);
    if(!strcmp(tag, "TXX")) sprintf(m_chbuf, "User defined text information frame: %s", value);
    if(!strcmp(tag, "TYE")) sprintf(m_chbuf, "Year: %s", value);
    if(!strcmp(tag, "UFI")) sprintf(m_chbuf, "Unique file identifier: %s", value);
    if(!strcmp(tag, "ULT")) sprintf(m_chbuf, "Unsychronized lyric/text transcription: %s", value);
    if(!strcmp(tag, "WAF")) sprintf(m_chbuf, "Official audio file webpage: %s", value);
    if(!strcmp(tag, "WAR")) sprintf(m_chbuf, "Official artist/performer webpage: %s", value);
    if(!strcmp(tag, "WAS")) sprintf(m_chbuf, "Official audio source webpage: %s", value);
    if(!strcmp(tag, "WCM")) sprintf(m_chbuf, "Commercial information: %s", value);
    if(!strcmp(tag, "WCP")) sprintf(m_chbuf, "Copyright/Legal information: %s", value);
    if(!strcmp(tag, "WPB")) sprintf(m_chbuf, "Publishers official webpage: %s", value);
    if(!strcmp(tag, "WXX")) sprintf(m_chbuf, "User defined URL link frame: %s", value);

    // V2.3 V2.4 tags
    // if(!strcmp(tag, "COMM")) sprintf(m_chbuf, "Comment: %s", value);
    if(!strcmp(tag, "OWNE")) sprintf(m_chbuf, "Ownership: %s", value);
    // if(!strcmp(tag, "PRIV")) sprintf(m_chbuf, "Private: %s", value);
    if(!strcmp(tag, "SYLT")) sprintf(m_chbuf, "SynLyrics: %s", value);
    if(!strcmp(tag, "TALB")) sprintf(m_chbuf, "Album: %s", value);
    if(!strcmp(tag, "TBPM")) sprintf(m_chbuf, "BeatsPerMinute: %s", value);
    if(!strcmp(tag, "TCMP")) sprintf(m_chbuf, "Compilation: %s", value);
    if(!strcmp(tag, "TCOM")) sprintf(m_chbuf, "Composer: %s", value);
    if(!strcmp(tag, "TCON")) sprintf(m_chbuf, "ContentType: %s", value);
    if(!strcmp(tag, "TCOP")) sprintf(m_chbuf, "Copyright: %s", value);
    if(!strcmp(tag, "TDAT")) sprintf(m_chbuf, "Date: %s", value);
    if(!strcmp(tag, "TEXT")) sprintf(m_chbuf, "Lyricist: %s", value);
    if(!strcmp(tag, "TIME")) sprintf(m_chbuf, "Time: %s", value);
    if(!strcmp(tag, "TIT1")) sprintf(m_chbuf, "Grouping: %s", value);
    if(!strcmp(tag, "TIT2")) sprintf(m_chbuf, "Title: %s", value);
    if(!strcmp(tag, "TIT3")) sprintf(m_chbuf, "Subtitle: %s", value);
    if(!strcmp(tag, "TLAN")) sprintf(m_chbuf, "Language: %s", value);
    if(!strcmp(tag, "TLEN")) sprintf(m_chbuf, "Length (ms): %s", value);
    if(!strcmp(tag, "TMED")) sprintf(m_chbuf, "Media: %s", value);
    if(!strcmp(tag, "TOAL")) sprintf(m_chbuf, "OriginalAlbum: %s", value);
    if(!strcmp(tag, "TOPE")) sprintf(m_chbuf, "OriginalArtist: %s", value);
    if(!strcmp(tag, "TORY")) sprintf(m_chbuf, "OriginalReleaseYear: %s", value);
    if(!strcmp(tag, "TPE1")) sprintf(m_chbuf, "Artist: %s", value);
    if(!strcmp(tag, "TPE2")) sprintf(m_chbuf, "Band: %s", value);
    if(!strcmp(tag, "TPE3")) sprintf(m_chbuf, "Conductor: %s", value);
    if(!strcmp(tag, "TPE4")) sprintf(m_chbuf, "InterpretedBy: %s", value);
    if(!strcmp(tag, "TPOS")) sprintf(m_chbuf, "PartOfSet: %s", value);
    if(!strcmp(tag, "TPUB")) sprintf(m_chbuf, "Publisher: %s", value);
    if(!strcmp(tag, "TRCK")) sprintf(m_chbuf, "Track: %s", value);
    if(!strcmp(tag, "TSSE")) sprintf(m_chbuf, "SettingsForEncoding: %s", value);
    if(!strcmp(tag, "TRDA")) sprintf(m_chbuf, "RecordingDates: %s", value);
    if(!m_f_m3u8data)
    if(!strcmp(tag, "TXXX")) sprintf(m_chbuf, "UserDefinedText: %s", value);
    if(!strcmp(tag, "TYER")) sprintf(m_chbuf, "Year: %s", value);
    if(!strcmp(tag, "USER")) sprintf(m_chbuf, "TermsOfUse: %s", value);
    if(!strcmp(tag, "USLT")) sprintf(m_chbuf, "Lyrics: %s", value);
    if(!strcmp(tag, "WOAR")) sprintf(m_chbuf, "OfficialArtistWebpage: %s", value);
    if(!strcmp(tag, "XDOR")) sprintf(m_chbuf, "OriginalReleaseTime: %s", value);

    latinToUTF8(m_chbuf, sizeof(m_chbuf));
    if(indexOf(m_chbuf, "?xml", 0) > 0) {
        showstreamtitle(m_chbuf);
        return;
    }
    if(m_chbuf[0] != 0) {
        if(audio_id3data) audio_id3data(m_chbuf);
    }
}
//------------------------------------------------------------------------------------------------------------------------------------------------------------------------------------------------------
void Audio::unicode2utf8(char* buff, uint32_t len) {
    // converts unicode in UTF-8, buff contains the string to be converted up to len
    // range U+1 ... U+FFFF
    uint8_t* tmpbuff = (uint8_t*)malloc(len * 2);
    if(!tmpbuff) {
        log_e("out of memory");
        return;
    }
    bool     bitorder = false;
    uint16_t j = 0;
    uint16_t k = 0;
    uint16_t m = 0;
    uint8_t  uni_h = 0;
    uint8_t  uni_l = 0;

    while(m < len - 1) {
        if((buff[m] == 0xFE) && (buff[m + 1] == 0xFF)) {
            bitorder = true;
            j = m + 2;
        } // LSB/MSB
        if((buff[m] == 0xFF) && (buff[m + 1] == 0xFE)) {
            bitorder = false;
            j = m + 2;
        } // MSB/LSB
        m++;
    } // seek for last bitorder
    m = 0;
    if(j > 0) {
        for(k = j; k < len; k += 2) {
            if(bitorder == true) {
                uni_h = (uint8_t)buff[k];
                uni_l = (uint8_t)buff[k + 1];
            }
            else {
                uni_l = (uint8_t)buff[k];
                uni_h = (uint8_t)buff[k + 1];
            }

            uint16_t uni_hl = ((uni_h << 8) | uni_l);

            if(uni_hl < 0X80) {
                tmpbuff[m] = uni_l;
                m++;
            }
            else if(uni_hl < 0X800) {
                tmpbuff[m] = ((uni_hl >> 6) | 0XC0);
                m++;
                tmpbuff[m] = ((uni_hl & 0X3F) | 0X80);
                m++;
            }
            else {
                tmpbuff[m] = ((uni_hl >> 12) | 0XE0);
                m++;
                tmpbuff[m] = (((uni_hl >> 6) & 0X3F) | 0X80);
                m++;
                tmpbuff[m] = ((uni_hl & 0X3F) | 0X80);
                m++;
            }
        }
    }
    memcpy(buff, tmpbuff, m);
    buff[m] = 0;
    if(tmpbuff) {
        free(tmpbuff);
        tmpbuff = NULL;
    }
}
//------------------------------------------------------------------------------------------------------------------------------------------------------------------------------------------------------
bool Audio::latinToUTF8(char* buff, size_t bufflen, bool UTF8check) {
    // most stations send  strings in UTF-8 but a few sends in latin. To standardize this, all latin strings are
    // converted to UTF-8. If UTF-8 is already present, nothing is done and true is returned.
    // A conversion to UTF-8 extends the string. Therefore it is necessary to know the buffer size. If the converted
    // string does not fit into the buffer, false is returned

    bool     isUTF8 = true;  // assume UTF8
    uint16_t pos = 0;
    uint16_t in = 0;
    uint16_t out = 0;
    uint16_t len = strlen(buff);
    uint8_t  c;

    // We cannot detect if a given string (or byte sequence) is a UTF-8 encoded text as for example each and every series
    // of UTF-8 octets is also a valid (if nonsensical) series of Latin-1 (or some other encoding) octets.
    // However not every series of valid Latin-1 octets are valid UTF-8 series. So you can rule out strings that do not conform
    // to the UTF-8 encoding schema:

    if(UTF8check){
        while(pos < len) {  // check first, if we have a clear UTF-8 string
            c = buff[pos];
            if(c >= 0xC2 && c <= 0xDF) { // may be 2 bytes UTF8, e.g. 0xC2B5 is 'µ' (MICRO SIGN)
                if(pos + 1 == len){
                    isUTF8 = false;
                    break;
                }
                if(buff[pos + 1] < 0x80){
                    isUTF8 = false;
                    break;
                }
                pos += 2;
                continue;
            }
            if(c >= 0xE0 && c <= 0xEF){ // may  be 3 bytes UTF8, e.g. 0xE0A484 is 'ऄ' (DEVANAGARI LETTER SHORT A)
                if(pos + 2 >= len){ //
                    isUTF8 = false;
                    break;
                }
                if(buff[pos + 1] < 0x80 || buff[pos + 2] < 0x80){
                    isUTF8 = false;
                    break;
                }
                pos += 3;
                continue;
            }
            if(c >= 0xF0){ // may  be 4 bytes UTF8, e.g. 0xF0919AA6 (TAKRI LETTER VA)
                if(pos + 3 >= len){ //
                    isUTF8 = false;
                    break;
                }
                if(buff[pos + 1] < 0x80 || buff[pos + 2] < 0x80 || buff[pos + 3] < 0x80){
                    isUTF8 = false;
                    break;
                }
                pos += 4;
                continue;
            }
            pos++;
        }
        if(isUTF8 == true) return true; // is UTF-8, do nothing
    }

    char* iso8859_1 = x_strdup(buff);
    if(!iso8859_1){log_e("oom"); return false;}

    while(iso8859_1[in] != '\0'){
        if(iso8859_1[in] < 0x80){
            buff[out] = iso8859_1[in];
            out++;
            in++;
            if(out > bufflen) goto exit;
        }
        else{
            buff[out] = (0xC0 | iso8859_1[in] >> 6);
            out++;
            if(out + 1 > bufflen) goto exit;
            buff[out] = (0x80 | (iso8859_1[in] & 0x3F));
            out++;
            in++;
        }
    }
    buff[out] = '\0';
    if(iso8859_1) {free(iso8859_1); iso8859_1 = NULL;}
    return true;

exit:
    if(iso8859_1) {free(iso8859_1); iso8859_1 = NULL;}
    return false;
}
//------------------------------------------------------------------------------------------------------------------------------------------------------------------------------------------------------
size_t Audio::readAudioHeader(uint32_t bytes) {
    size_t bytesReaded = 0;
    if(m_codec == CODEC_WAV) {
        int res = read_WAV_Header(InBuff.getReadPtr(), bytes);
        if(res >= 0) bytesReaded = res;
        else { // error, skip header
            m_controlCounter = 100;
        }
    }
    if(m_codec == CODEC_MP3) {
        int res = read_ID3_Header(InBuff.getReadPtr(), bytes);
        if(res >= 0) bytesReaded = res;
        else { // error, skip header
            m_controlCounter = 100;
        }
    }
    if(m_codec == CODEC_M4A) {
        int res = read_M4A_Header(InBuff.getReadPtr(), bytes);
        if(res >= 0) bytesReaded = res;
        else { // error, skip header
            m_controlCounter = 100;
        }
    }
    if(m_codec == CODEC_AAC) {
        // stream only, no header
        m_audioDataSize = getFileSize();
        m_controlCounter = 100;
    }
    if(m_codec == CODEC_FLAC) {
        int res = read_FLAC_Header(InBuff.getReadPtr(), bytes);
        if(res >= 0) bytesReaded = res;
        else { // error, skip header
            stopSong();
            m_controlCounter = 100;
        }
    }
    if(m_codec == CODEC_OPUS) { m_controlCounter = 100; }
    if(m_codec == CODEC_VORBIS) { m_controlCounter = 100; }
    if(m_codec == CODEC_OGG) { m_controlCounter = 100; }
    if(!isRunning()) {
        log_e("Processing stopped due to invalid audio header");
        return 0;
    }
    return bytesReaded;
}
//------------------------------------------------------------------------------------------------------------------------------------------------------------------------------------------------------
int Audio::read_WAV_Header(uint8_t* data, size_t len) {
    static size_t   headerSize;
    static uint32_t cs = 0;
    static uint8_t  bts = 0;

    if(m_controlCounter == 0) {
        m_controlCounter++;
        if((*data != 'R') || (*(data + 1) != 'I') || (*(data + 2) != 'F') || (*(data + 3) != 'F')) {
            AUDIO_INFO("file has no RIFF tag");
            headerSize = 0;
            return -1; // false;
        }
        else {
            headerSize = 4;
            return 4; // ok
        }
    }

    if(m_controlCounter == 1) {
        m_controlCounter++;
        cs = (uint32_t)(*data + (*(data + 1) << 8) + (*(data + 2) << 16) + (*(data + 3) << 24) - 8);
        headerSize += 4;
        return 4; // ok
    }

    if(m_controlCounter == 2) {
        m_controlCounter++;
        if((*data != 'W') || (*(data + 1) != 'A') || (*(data + 2) != 'V') || (*(data + 3) != 'E')) {
            AUDIO_INFO("format tag is not WAVE");
            return -1; // false;
        }
        else {
            headerSize += 4;
            return 4;
        }
    }

    if(m_controlCounter == 3) {
        if((*data == 'f') && (*(data + 1) == 'm') && (*(data + 2) == 't')) {
            m_controlCounter++;
            headerSize += 4;
            return 4;
        }
        else {
            headerSize += 4;
            return 4;
        }
    }

    if(m_controlCounter == 4) {
        m_controlCounter++;
        cs = (uint32_t)(*data + (*(data + 1) << 8));
        if(cs > 40) return -1; // false, something going wrong
        bts = cs - 16;         // bytes to skip if fmt chunk is >16
        headerSize += 4;
        return 4;
    }

    if(m_controlCounter == 5) {
        m_controlCounter++;
        uint16_t fc = (uint16_t)(*(data + 0) + (*(data + 1) << 8));                                               // Format code
        uint16_t nic = (uint16_t)(*(data + 2) + (*(data + 3) << 8));                                              // Number of interleaved channels
        uint32_t sr = (uint32_t)(*(data + 4) + (*(data + 5) << 8) + (*(data + 6) << 16) + (*(data + 7) << 24));   // Samplerate
        uint32_t dr = (uint32_t)(*(data + 8) + (*(data + 9) << 8) + (*(data + 10) << 16) + (*(data + 11) << 24)); // Datarate
        uint16_t dbs = (uint16_t)(*(data + 12) + (*(data + 13) << 8));                                            // Data block size
        uint16_t bps = (uint16_t)(*(data + 14) + (*(data + 15) << 8));                                            // Bits per sample

        AUDIO_INFO("FormatCode: %u", fc);
        // AUDIO_INFO("Channel: %u", nic);
        // AUDIO_INFO("SampleRate: %u", sr);
        AUDIO_INFO("DataRate: %lu", (long unsigned int)dr);
        AUDIO_INFO("DataBlockSize: %u", dbs);
        AUDIO_INFO("BitsPerSample: %u", bps);

        if((bps != 8) && (bps != 16)) {
            AUDIO_INFO("BitsPerSample is %u,  must be 8 or 16", bps);
            stopSong();
            return -1;
        }
        if((nic != 1) && (nic != 2)) {
            AUDIO_INFO("num channels is %u,  must be 1 or 2", nic);
            stopSong();
            return -1;
        }
        if(fc != 1) {
            AUDIO_INFO("format code is not 1 (PCM)");
            stopSong();
            return -1; // false;
        }
        setBitsPerSample(bps);
        setChannels(nic);
        setSampleRate(sr);
        setBitrate(nic * sr * bps);
        //    AUDIO_INFO("BitRate: %u", m_bitRate);
        headerSize += 16;
        return 16; // ok
    }

    if(m_controlCounter == 6) {
        m_controlCounter++;
        headerSize += bts;
        return bts; // skip to data
    }

    if(m_controlCounter == 7) {
        if((*(data + 0) == 'd') && (*(data + 1) == 'a') && (*(data + 2) == 't') && (*(data + 3) == 'a')) {
            m_controlCounter++;
            //    vTaskDelay(30);
            headerSize += 4;
            return 4;
        }
        else {
            headerSize++;
            return 1;
        }
    }

    if(m_controlCounter == 8) {
        m_controlCounter++;
        size_t cs = *(data + 0) + (*(data + 1) << 8) + (*(data + 2) << 16) + (*(data + 3) << 24); // read chunkSize
        headerSize += 4;
        if(getDatamode() == AUDIO_LOCALFILE) m_contentlength = getFileSize();
        if(cs) { m_audioDataSize = cs - 44; }
        else { // sometimes there is nothing here
            if(getDatamode() == AUDIO_LOCALFILE) m_audioDataSize = getFileSize() - headerSize;
            if(m_streamType == ST_WEBFILE) m_audioDataSize = m_contentlength - headerSize;
        }
        AUDIO_INFO("Audio-Length: %u", m_audioDataSize);
        return 4;
    }
    m_controlCounter = 100; // header succesfully read
    m_audioDataStart = headerSize;
    return 0;
}
//------------------------------------------------------------------------------------------------------------------------------------------------------------------------------------------------------
int Audio::read_FLAC_Header(uint8_t* data, size_t len) {
    static size_t   headerSize;
    static size_t   retvalue = 0;
    static bool     f_lastMetaBlock = false;
    static uint32_t picPos = 0;
    static uint32_t picLen = 0;

    if(retvalue) {
        if(retvalue > len) { // if returnvalue > bufferfillsize
            if(len > InBuff.getMaxBlockSize()) len = InBuff.getMaxBlockSize();
            retvalue -= len; // and wait for more bufferdata
            return len;
        }
        else {
            size_t tmp = retvalue;
            retvalue = 0;
            return tmp;
        }
        return 0;
    }
    // - - - - - - - - - - - - - - - - - - - - - - - - - - - - - - - - - - - - - - - -
    if(m_controlCounter == FLAC_BEGIN) { // init
        headerSize = 0;
        retvalue = 0;
        m_audioDataStart = 0;
        picPos = 0;
        picLen = 0;
        f_lastMetaBlock = false;
        m_controlCounter = FLAC_MAGIC;
        if(getDatamode() == AUDIO_LOCALFILE) {
            m_contentlength = getFileSize();
            AUDIO_INFO("Content-Length: %lu", (long unsigned int)m_contentlength);
        }
        return 0;
    }
    // - - - - - - - - - - - - - - - - - - - - - - - - - - - - - - - - - - - - - - - -
    if(m_controlCounter == FLAC_MAGIC) {            /* check MAGIC STRING */
        if(specialIndexOf(data, "OggS", 10) == 0) { // is ogg
            headerSize = 0;
            retvalue = 0;
            m_controlCounter = FLAC_OKAY;
            return 0;
        }
        if(specialIndexOf(data, "fLaC", 10) != 0) {
            log_e("Magic String 'fLaC' not found in header");
            stopSong();
            return -1;
        }
        m_controlCounter = FLAC_MBH; // METADATA_BLOCK_HEADER
        headerSize = 4;
        retvalue = 4;
        return 0;
    }
    // - - - - - - - - - - - - - - - - - - - - - - - - - - - - - - - - - - - - - - - -
    if(m_controlCounter == FLAC_MBH) { /* METADATA_BLOCK_HEADER */
        uint8_t blockType = *data;
        if(!f_lastMetaBlock) {
            if(blockType & 128) { f_lastMetaBlock = true; }
            blockType &= 127;
            if(blockType == 0) m_controlCounter = FLAC_SINFO;
            if(blockType == 1) m_controlCounter = FLAC_PADDING;
            if(blockType == 2) m_controlCounter = FLAC_APP;
            if(blockType == 3) m_controlCounter = FLAC_SEEK;
            if(blockType == 4) m_controlCounter = FLAC_VORBIS;
            if(blockType == 5) m_controlCounter = FLAC_CUESHEET;
            if(blockType == 6) m_controlCounter = FLAC_PICTURE;
            headerSize += 1;
            retvalue = 1;
            return 0;
        }
        m_controlCounter = FLAC_OKAY;
        m_audioDataStart = headerSize;
        m_audioDataSize = m_contentlength - m_audioDataStart;
        FLACSetRawBlockParams(m_flacNumChannels, m_flacSampleRate, m_flacBitsPerSample, m_flacTotalSamplesInStream, m_audioDataSize);
        if(picLen) {
            size_t pos = audiofile.position();
            if(audio_id3image) audio_id3image(audiofile, picPos, picLen);
            audiofile.seek(pos); // the filepointer could have been changed by the user, set it back
        }
        AUDIO_INFO("Audio-Length: %u", m_audioDataSize);
        retvalue = 0;
        return 0;
    }
    // - - - - - - - - - - - - - - - - - - - - - - - - - - - - - - - - - - - - - - - -
    if(m_controlCounter == FLAC_SINFO) { /* Stream info block */
        size_t l = bigEndian(data, 3);
        vTaskDelay(2);
        m_flacMaxBlockSize = bigEndian(data + 5, 2);
        AUDIO_INFO("FLAC maxBlockSize: %u", m_flacMaxBlockSize);
        vTaskDelay(2);
        m_flacMaxFrameSize = bigEndian(data + 10, 3);
        if(m_flacMaxFrameSize) { AUDIO_INFO("FLAC maxFrameSize: %u", m_flacMaxFrameSize); }
        else { AUDIO_INFO("FLAC maxFrameSize: N/A"); }
        if(m_flacMaxFrameSize > InBuff.getMaxBlockSize()) {
            log_e("FLAC maxFrameSize too large!");
            stopSong();
            return -1;
        }
        //        InBuff.changeMaxBlockSize(m_flacMaxFrameSize);
        vTaskDelay(2);
        uint32_t nextval = bigEndian(data + 13, 3);
        m_flacSampleRate = nextval >> 4;
        AUDIO_INFO("FLAC sampleRate: %lu", (long unsigned int)m_flacSampleRate);
        vTaskDelay(2);
        m_flacNumChannels = ((nextval & 0x06) >> 1) + 1;
        AUDIO_INFO("FLAC numChannels: %u", m_flacNumChannels);
        vTaskDelay(2);
        uint8_t bps = (nextval & 0x01) << 4;
        bps += (*(data + 16) >> 4) + 1;
        m_flacBitsPerSample = bps;
        if((bps != 8) && (bps != 16)) {
            log_e("bits per sample must be 8 or 16, is %i", bps);
            stopSong();
            return -1;
        }
        AUDIO_INFO("FLAC bitsPerSample: %u", m_flacBitsPerSample);
        m_flacTotalSamplesInStream = bigEndian(data + 17, 4);
        if(m_flacTotalSamplesInStream) { AUDIO_INFO("total samples in stream: %lu", (long unsigned int)m_flacTotalSamplesInStream); }
        else { AUDIO_INFO("total samples in stream: N/A"); }
        if(bps != 0 && m_flacTotalSamplesInStream) { AUDIO_INFO("audio file duration: %lu seconds", (long unsigned int)m_flacTotalSamplesInStream / (long unsigned int)m_flacSampleRate); }
        m_controlCounter = FLAC_MBH; // METADATA_BLOCK_HEADER
        retvalue = l + 3;
        headerSize += retvalue;
        return 0;
    }
    // - - - - - - - - - - - - - - - - - - - - - - - - - - - - - - - - - - - - - - - -
    if(m_controlCounter == FLAC_PADDING) { /* PADDING */
        size_t l = bigEndian(data, 3);
        m_controlCounter = FLAC_MBH;
        retvalue = l + 3;
        headerSize += retvalue;
        return 0;
    }
    // - - - - - - - - - - - - - - - - - - - - - - - - - - - - - - - - - - - - - - - -
    if(m_controlCounter == FLAC_APP) { /* APPLICATION */
        size_t l = bigEndian(data, 3);
        m_controlCounter = FLAC_MBH;
        retvalue = l + 3;
        headerSize += retvalue;
        return 0;
    }
    // - - - - - - - - - - - - - - - - - - - - - - - - - - - - - - - - - - - - - - - -
    if(m_controlCounter == FLAC_SEEK) { /* SEEKTABLE */
        size_t l = bigEndian(data, 3);
        m_controlCounter = FLAC_MBH;
        retvalue = l + 3;
        headerSize += retvalue;
        return 0;
    }
    // - - - - - - - - - - - - - - - - - - - - - - - - - - - - - - - - - - - - - - - -
    if(m_controlCounter == FLAC_VORBIS) { /* VORBIS COMMENT */ // field names
        size_t vendorLength = bigEndian(data, 3);
        size_t idx = 0;
        data += 3; idx += 3;
        size_t vendorStringLength = data[0] + (data[1] << 8) + (data[2] << 16) + (data[3] << 24);
        if(vendorStringLength) {data += 4; idx += 4;}
        if(vendorStringLength > 495) vendorStringLength = 495; // guard
        strcpy(m_chbuf, "VENDOR_STRING: ");
        strncpy(m_chbuf + 15, (const char*)data, vendorStringLength);
        m_chbuf[15 + vendorStringLength] = '\0';
        if(audio_id3data) audio_id3data(m_chbuf);
        data += vendorStringLength; idx += vendorStringLength;
        size_t commentListLength = data[0] + (data[1] << 8) + (data[2] << 16) + (data[3] << 24);
        data += 4; idx += 4;

        for(int i = 0; i < commentListLength; i++) {
            (void)i;
            size_t commentLength = data[0] + (data[1] << 8) + (data[2] << 16) + (data[3] << 24);
            data += 4; idx += 4;
            if(commentLength < 512) { // guard
                strncpy(m_chbuf, (const char *)data , commentLength);
                m_chbuf[commentLength] = '\0';
                if(audio_id3data) audio_id3data(m_chbuf);
            }
            data += commentLength; idx += commentLength;
            if(idx > vendorLength + 3) {log_e("VORBIS COMMENT section is too long");}
        }
        m_controlCounter = FLAC_MBH;
        retvalue = vendorLength + 3;
        headerSize += retvalue;
        return 0;
    }
    // - - - - - - - - - - - - - - - - - - - - - - - - - - - - - - - - - - - - - - - -
    if(m_controlCounter == FLAC_CUESHEET) { /* CUESHEET */
        size_t l = bigEndian(data, 3);
        m_controlCounter = FLAC_MBH;
        retvalue = l + 3;
        headerSize += retvalue;
        return 0;
    }
    // - - - - - - - - - - - - - - - - - - - - - - - - - - - - - - - - - - - - - - - -
    if(m_controlCounter == FLAC_PICTURE) { /* PICTURE */
        picLen = bigEndian(data, 3);
        picPos = headerSize;
        // log_w("FLAC PICTURE, size %i, pos %i", picLen, picPos);
        m_controlCounter = FLAC_MBH;
        retvalue = picLen + 3;
        headerSize += retvalue;
        return 0;
    }
    return 0;
}
//------------------------------------------------------------------------------------------------------------------------------------------------------------------------------------------------------
int Audio::read_ID3_Header(uint8_t* data, size_t len) {
    static size_t   id3Size;
    static size_t   totalId3Size; // if we have more header, id3_1_size + id3_2_size + ....
    static size_t   remainingHeaderBytes;
    static size_t   universal_tmp = 0;
    static uint8_t  ID3version;
    static int      ehsz = 0;
    static char     tag[5];
    static char     frameid[5];
    static size_t   framesize = 0;
    static bool     compressed = false;
    static size_t   APIC_size[3] = {0};
    static uint32_t APIC_pos[3] = {0};
    static bool     SYLT_seen = false;
    static size_t   SYLT_size = 0;
    static uint32_t SYLT_pos = 0;
    static uint8_t  numID3Header = 0;
    // - - - - - - - - - - - - - - - - - - - - - - - - - - - - - - - - - - - - - - - -
    if(m_controlCounter == 0) { /* read ID3 tag and ID3 header size */
        if(getDatamode() == AUDIO_LOCALFILE) {
            ID3version = 0;
            m_contentlength = getFileSize();
            AUDIO_INFO("Content-Length: %lu", (long unsigned int)m_contentlength);
        }
        m_controlCounter++;
        SYLT_seen = false;
        remainingHeaderBytes = 0;
        ehsz = 0;
        if(specialIndexOf(data, "ID3", 4) != 0) { // ID3 not found
            if(!m_f_m3u8data) AUDIO_INFO("file has no mp3 tag, skip metadata");
            m_audioDataSize = m_contentlength;
            if(!m_f_m3u8data) AUDIO_INFO("Audio-Length: %u", m_audioDataSize);
            return -1; // error, no ID3 signature found
        }
        ID3version = *(data + 3);
        switch(ID3version) {
            case 2:
                m_f_unsync = (*(data + 5) & 0x80);
                m_f_exthdr = false;
                break;
            case 3:
            case 4:
                m_f_unsync = (*(data + 5) & 0x80); // bit7
                m_f_exthdr = (*(data + 5) & 0x40); // bit6 extended header
                break;
        };
        id3Size = bigEndian(data + 6, 4, 7); //  ID3v2 size  4 * %0xxxxxxx (shift left seven times!!)
        id3Size += 10;

        // Every read from now may be unsync'd
        if(!m_f_m3u8data) AUDIO_INFO("ID3 framesSize: %i", id3Size);
        if(!m_f_m3u8data) AUDIO_INFO("ID3 version: 2.%i", ID3version);

        if(ID3version == 2) { m_controlCounter = 10; }
        remainingHeaderBytes = id3Size;
        m_ID3Size = id3Size;
        remainingHeaderBytes -= 10;

        return 10;
    }
    // - - - - - - - - - - - - - - - - - - - - - - - - - - - - - - - - - - - - - - - -
    if(m_controlCounter == 1) { // compute extended header size if exists
        m_controlCounter++;
        if(m_f_exthdr) {
            AUDIO_INFO("ID3 extended header");
            ehsz = bigEndian(data, 4);
            remainingHeaderBytes -= 4;
            ehsz -= 4;
            return 4;
        }
        else {
            if(!m_f_m3u8data) AUDIO_INFO("ID3 normal frames");
            return 0;
        }
    }
    // - - - - - - - - - - - - - - - - - - - - - - - - - - - - - - - - - - - - - - - -
    if(m_controlCounter == 2) { // skip extended header if exists
        if(ehsz > len) {
            ehsz -= len;
            remainingHeaderBytes -= len;
            return len;
        } // Throw it away
        else {
            m_controlCounter++;
            remainingHeaderBytes -= ehsz;
            return ehsz;
        } // Throw it away
    }
    // - - - - - - - - - - - - - - - - - - - - - - - - - - - - - - - - - - - - - - - -
    if(m_controlCounter == 3) { // read a ID3 frame, get the tag
        if(remainingHeaderBytes == 0) {
            m_controlCounter = 99;
            return 0;
        }
        m_controlCounter++;
        frameid[0] = *(data + 0);
        frameid[1] = *(data + 1);
        frameid[2] = *(data + 2);
        frameid[3] = *(data + 3);
        frameid[4] = 0;
        for(uint8_t i = 0; i < 4; i++) tag[i] = frameid[i]; // tag = frameid

        remainingHeaderBytes -= 4;
        if(frameid[0] == 0 && frameid[1] == 0 && frameid[2] == 0 && frameid[3] == 0) {
            // We're in padding
            m_controlCounter = 98; // all ID3 metadata processed
        }
        return 4;
    }
    // - - - - - - - - - - - - - - - - - - - - - - - - - - - - - - - - - - - - - - - -
    if(m_controlCounter == 4) { // get the frame size
        m_controlCounter = 6;

        if(ID3version == 4) {
            framesize = bigEndian(data, 4, 7); // << 7
        }
        else {
            framesize = bigEndian(data, 4); // << 8
        }
        remainingHeaderBytes -= 4;
        uint8_t flag = *(data + 4); // skip 1st flag
        (void)flag;
        remainingHeaderBytes--;
        compressed = (*(data + 5)) & 0x80; // Frame is compressed using [#ZLIB zlib] with 4 bytes for 'decompressed
                                           // size' appended to the frame header.
        remainingHeaderBytes--;
        uint32_t decompsize = 0;
        if(compressed) {
            if(m_f_Log) log_i("iscompressed");
            decompsize = bigEndian(data + 6, 4);
            remainingHeaderBytes -= 4;
            (void)decompsize;
            if(m_f_Log) log_i("decompsize=%u", decompsize);
            return 6 + 4;
        }
        return 6;
    }
    // - - - - - - - - - - - - - - - - - - - - - - - - - - - - - - - - - - - - - - - -
    if(m_controlCounter == 5) { // If the frame is larger than 512 bytes, skip the rest
        if(framesize > len) {
            framesize -= len;
            remainingHeaderBytes -= len;
            return len;
        }
        else {
            m_controlCounter = 3; // check next frame
            remainingHeaderBytes -= framesize;
            return framesize;
        }
    }
    // - - - - - - - - - - - - - - - - - - - - - - - - - - - - - - - - - - - - - - - -
    if(m_controlCounter == 6) { // Read the value
        m_controlCounter = 5;   // only read 256 bytes
        char ch = *(data + 0);
        // $00 – ISO-8859-1 (LATIN-1, Identical to ASCII for values smaller than 0x80).
        // $01 – UCS-2 encoded Unicode with BOM, in ID3v2.2 and ID3v2.3.
        // $02 – UTF-16BE encoded Unicode without BOM, in ID3v2.4.
        // $03 – UTF-8 encoded Unicode, in ID3v2.4.
        bool isUnicode = (ch == 1) ? true : false;

        if(startsWith(tag, "APIC")) { // a image embedded in file, passing it to external function
            isUnicode = false;
            if(getDatamode() == AUDIO_LOCALFILE) {
                APIC_pos[numID3Header] = totalId3Size + id3Size - remainingHeaderBytes;
                APIC_size[numID3Header] = framesize;
                //    log_e("APIC_pos %i APIC_size %i", APIC_pos[numID3Header], APIC_size[numID3Header]);
            }
            return 0;
        }

        if( // any lyrics embedded in file, passing it to external function
            startsWith(tag, "SYLT") || startsWith(tag, "TXXX") || startsWith(tag, "USLT")) {
            if(getDatamode() == AUDIO_LOCALFILE) {
                SYLT_seen = true;
                SYLT_pos = id3Size - remainingHeaderBytes;
                SYLT_size = framesize;
            }
            return 0;
        }

        size_t fs = framesize;
        if(fs > 1024) fs = 1024;
        for(int i = 0; i < fs; i++) { m_ibuff[i] = *(data + i); }
        framesize -= fs;
        remainingHeaderBytes -= fs;
        m_ibuff[fs] = 0;

        if(isUnicode && fs > 1) {
            unicode2utf8(m_ibuff, fs); // convert unicode to utf-8 U+0020...U+07FF
        }

        if(!isUnicode) {
            uint16_t j = 0, k = 0;
            while(j < fs) {
                if(m_ibuff[j] > 0x1F) {
                    m_ibuff[k] = m_ibuff[j]; // remove non printables
                    k++;
                }
                j++;
            }
            m_ibuff[k] = '\0'; // new termination
            latinToUTF8(m_ibuff, m_ibuffSize, false);
        }
        showID3Tag(tag, m_ibuff);
        return fs;
    }
    // - - - - - - - - - - - - - - - - - - - - - - - - - - - - - - - - - - - - - - - -

    // --- section V2.2 only , greater Vers above ----
    // see https://mutagen-specs.readthedocs.io/en/latest/id3/id3v2.2.html
    if(m_controlCounter == 10) { // frames in V2.2, 3bytes identifier, 3bytes size descriptor

        if(universal_tmp > 0) {
            if(universal_tmp > 256) {
                universal_tmp -= 256;
                return 256;
            }
            else {
                uint8_t t = universal_tmp;
                universal_tmp = 0;
                return t;
            }
        }

        frameid[0] = *(data + 0);
        frameid[1] = *(data + 1);
        frameid[2] = *(data + 2);
        frameid[3] = 0;
        for(uint8_t i = 0; i < 4; i++) tag[i] = frameid[i]; // tag = frameid
        remainingHeaderBytes -= 3;
        size_t dataLen = bigEndian(data + 3, 3);
        universal_tmp = dataLen;
        remainingHeaderBytes -= 3;
        char value[256];
        if(dataLen > 249) { dataLen = 249; }
        memcpy(value, (data + 7), dataLen);
        value[dataLen + 1] = 0;
        m_chbuf[0] = 0;
        if(startsWith(tag, "PIC")) { // image embedded in header
            if(getDatamode() == AUDIO_LOCALFILE) {
                APIC_pos[numID3Header] = id3Size - remainingHeaderBytes;
                APIC_size[numID3Header] = universal_tmp;
                if(m_f_Log) log_i("Attached picture seen at pos %d length %d", APIC_pos[0], APIC_size[0]);
            }
        }
        else if(startsWith(tag, "SLT")) { // lyrics embedded in header
            if(getDatamode() == AUDIO_LOCALFILE) {
                SYLT_seen = true; // #460
                SYLT_pos = id3Size - remainingHeaderBytes;
                SYLT_size = universal_tmp;
                if(m_f_Log) log_i("Attached lyrics seen at pos %d length %d", SYLT_pos, SYLT_size);
            }
        }
        else { showID3Tag(tag, value); }
        remainingHeaderBytes -= universal_tmp;
        universal_tmp -= dataLen;

        if(dataLen == 0) m_controlCounter = 98;
        if(remainingHeaderBytes == 0) m_controlCounter = 98;

        return 3 + 3 + dataLen;
    }
    // -- end section V2.2 -----------

    // - - - - - - - - - - - - - - - - - - - - - - - - - - - - - - - - - - - - - - - -
    if(m_controlCounter == 98) { // skip all ID3 metadata (mostly spaces)
        if(remainingHeaderBytes > len) {
            remainingHeaderBytes -= len;
            return len;
        } // Throw it away
        else {
            m_controlCounter = 99;
            return remainingHeaderBytes;
        } // Throw it away
    }
    // - - - - - - - - - - - - - - - - - - - - - - - - - - - - - - - - - - - - - - - -
    if(m_controlCounter == 99) { //  exist another ID3tag?
        m_audioDataStart += id3Size;
        //    vTaskDelay(30);
        if((*(data + 0) == 'I') && (*(data + 1) == 'D') && (*(data + 2) == '3')) {
            m_controlCounter = 0;
            numID3Header++;
            totalId3Size += id3Size;
            return 0;
        }
        else {
            m_controlCounter = 100; // ok
            m_audioDataSize = m_contentlength - m_audioDataStart;
            if(!m_f_m3u8data) AUDIO_INFO("Audio-Length: %u", m_audioDataSize);
            if(APIC_pos[0] && audio_id3image) { // if we have more than one APIC, output the first only
                size_t pos = audiofile.position();
                audio_id3image(audiofile, APIC_pos[0], APIC_size[0]);
                audiofile.seek(pos); // the filepointer could have been changed by the user, set it back
            }
            if(SYLT_seen && audio_id3lyrics) {
                size_t pos = audiofile.position();
                audio_id3lyrics(audiofile, SYLT_pos, SYLT_size);
                audiofile.seek(pos); // the filepointer could have been changed by the user, set it back
            }
            numID3Header = 0;
            totalId3Size = 0;
            for(int i = 0; i < 3; i++) APIC_pos[i] = 0;  // delete all
            for(int i = 0; i < 3; i++) APIC_size[i] = 0; // delete all
            return 0;
        }
    }
    return 0;
}
//------------------------------------------------------------------------------------------------------------------------------------------------------------------------------------------------------
int Audio::read_M4A_Header(uint8_t* data, size_t len) {
    /*
         ftyp
           | - moov  -> trak -> ... -> mp4a contains raw block parameters
           |    L... -> ilst  contains artist, composer ....
         free (optional) // jump to another atoms at the end of mdat
           |
         mdat contains the audio data                                                      */

    static size_t headerSize = 0;
    static size_t retvalue = 0;
    static size_t atomsize = 0;
    static size_t audioDataPos = 0;
    static uint32_t picPos = 0;
    static uint32_t picLen = 0;

    if(m_controlCounter == M4A_BEGIN) retvalue = 0;
    static size_t cnt = 0;
    if(retvalue) {
        if(len > InBuff.getMaxBlockSize()) len = InBuff.getMaxBlockSize();
        if(retvalue > len) { // if returnvalue > bufferfillsize
            retvalue -= len; // and wait for more bufferdata
            cnt += len;
            return len;
        }
        else {
            size_t tmp = retvalue;
            retvalue = 0;
            cnt += tmp;
            cnt = 0;
            return tmp;
        }
        return 0;
    }
    // - - - - - - - - - - - - - - - - - - - - - - - - - - - - - - - - - - - - - - - -
    if(m_controlCounter == M4A_BEGIN) { // init
        headerSize = 0;
        retvalue = 0;
        atomsize = 0;
        audioDataPos = 0;
        picPos = 0;
        picLen = 0;
        m_controlCounter = M4A_FTYP;
        return 0;
    }
    // - - - - - - - - - - - - - - - - - - - - - - - - - - - - - - - - - - - - - - - -
    if(m_controlCounter == M4A_FTYP) { /* check_m4a_file */
        atomsize = bigEndian(data, 4); // length of first atom
        if(specialIndexOf(data, "ftyp", 10) != 4) {
            log_e("atom 'ftyp' not found in header");
            stopSong();
            return -1;
        }
        int m4a = specialIndexOf(data, "M4A ", 20);
        int isom = specialIndexOf(data, "isom", 20);
        int mp42 = specialIndexOf(data, "mp42", 20);

        if((m4a != 8) && (isom != 8) && (mp42 != 8)) {
            log_e("subtype 'MA4 ', 'isom' or 'mp42' expected, but found '%s '", (data + 8));
            stopSong();
            return -1;
        }

        m_controlCounter = M4A_CHK;
        retvalue = atomsize;
        headerSize = atomsize;
        return 0;
    }
    // - - - - - - - - - - - - - - - - - - - - - - - - - - - - - - - - - - - - - - - -
    if(m_controlCounter == M4A_CHK) {  /* check  Tag */
        atomsize = bigEndian(data, 4); // length of this atom
        if(specialIndexOf(data, "moov", 10) == 4) {
            m_controlCounter = M4A_MOOV;
            return 0;
        }
        else if(specialIndexOf(data, "free", 10) == 4) {
            retvalue = atomsize;
            headerSize += atomsize;
            return 0;
        }
        else if(specialIndexOf(data, "mdat", 10) == 4) {
            m_controlCounter = M4A_MDAT;
            return 0;
        }
        else {
            char atomName[5] = {0};
            (void)atomName;
            atomName[0] = *data;
            atomName[1] = *(data + 1);
            atomName[2] = *(data + 2);
            atomName[3] = *(data + 3);
            atomName[4] = 0;

            if(m_f_Log) log_i("atom %s found", atomName);

            retvalue = atomsize;
            headerSize += atomsize;
            return 0;
        }
    }
    // - - - - - - - - - - - - - - - - - - - - - - - - - - - - - - - - - - - - - - - -
    if(m_controlCounter == M4A_MOOV) { // moov
        // we are looking for track and ilst
        if(specialIndexOf(data, "trak", len) > 0) {
            int offset = specialIndexOf(data, "trak", len);
            retvalue = offset;
            atomsize -= offset;
            headerSize += offset;
            m_controlCounter = M4A_TRAK;
            return 0;
        }
        if(specialIndexOf(data, "ilst", len) > 0) {
            int offset = specialIndexOf(data, "ilst", len);
            retvalue = offset;
            atomsize -= offset;
            headerSize += offset;
            m_controlCounter = M4A_ILST;
            return 0;
        }
        m_controlCounter = M4A_CHK;
        headerSize += atomsize;
        retvalue = atomsize;
        return 0;
    }
    // - - - - - - - - - - - - - - - - - - - - - - - - - - - - - - - - - - - - - - - -
    if(m_controlCounter == M4A_TRAK) { // trak
        if(specialIndexOf(data, "esds", len) > 0) {
            int      esds = specialIndexOf(data, "esds", len); // Packaging/Encapsulation And Setup Data
            uint8_t* pos = data + esds;
            uint8_t  len_of_OD = *(pos + 12); // length of this OD (which includes the next 2 tags)
            (void)len_of_OD;
            uint8_t len_of_ESD = *(pos + 20); // length of this Elementary Stream Descriptor
            (void)len_of_ESD;
            uint8_t audioType = *(pos + 21);

            if     (audioType == (uint8_t)0x40) { AUDIO_INFO("AudioType: MPEG4 / Audio"); } // ObjectTypeIndication
            else if(audioType == (uint8_t)0x66) { AUDIO_INFO("AudioType: MPEG2 / Audio"); }
            else if(audioType == (uint8_t)0x69) { AUDIO_INFO("AudioType: MPEG2 / Audio Part 3"); } // Backward Compatible Audio
            else if(audioType == (uint8_t)0x6B) { AUDIO_INFO("AudioType: MPEG1 / Audio"); }
            else { AUDIO_INFO("unknown Audio Type %x", audioType); }

            uint8_t streamType = *(pos + 22);
            streamType = streamType >> 2; // 6 bits
            if(streamType != 5) { log_e("Streamtype is not audio!"); }

            uint32_t maxBr = bigEndian(pos + 26, 4); // max bitrate
            AUDIO_INFO("max bitrate: %lu", (long unsigned int)maxBr);

            uint32_t avrBr = bigEndian(pos + 30, 4); // avg bitrate
            AUDIO_INFO("avr bitrate: %lu", (long unsigned int)avrBr);

            uint16_t ASC = bigEndian(pos + 39, 2);

            uint8_t objectType = ASC >> 11; // first 5 bits

            if     (objectType == 1) { AUDIO_INFO("AudioObjectType: AAC Main"); } // Audio Object Types
            else if(objectType == 2) { AUDIO_INFO("AudioObjectType: AAC Low Complexity"); }
            else if(objectType == 3) { AUDIO_INFO("AudioObjectType: AAC Scalable Sample Rate"); }
            else if(objectType == 4) { AUDIO_INFO("AudioObjectType: AAC Long Term Prediction"); }
            else if(objectType == 5) { AUDIO_INFO("AudioObjectType: AAC Spectral Band Replication"); }
            else if(objectType == 6) { AUDIO_INFO("AudioObjectType: AAC Scalable"); }
            else { AUDIO_INFO("unknown ObjectType %x, stop", objectType); stopSong();}

            const uint32_t samplingFrequencies[13] = {96000, 88200, 64000, 48000, 44100, 32000, 24000, 22050, 16000, 12000, 11025, 8000, 7350};
            uint8_t        sRate = (ASC & 0x0600) >> 7; // next 4 bits Sampling Frequencies
            AUDIO_INFO("Sampling Frequency: %lu", (long unsigned int)samplingFrequencies[sRate]);

            uint8_t chConfig = (ASC & 0x78) >> 3; // next 4 bits
            if(chConfig == 0) AUDIO_INFO("Channel Configurations: AOT Specifc Config");
            if(chConfig == 1) AUDIO_INFO("Channel Configurations: front-center");
            if(chConfig == 2) AUDIO_INFO("Channel Configurations: front-left, front-right");
            if(chConfig > 2) { log_e("Channel Configurations with more than 2 channels is not allowed, stop!"); stopSong();}

            uint8_t frameLengthFlag = (ASC & 0x04);
            uint8_t dependsOnCoreCoder = (ASC & 0x02);
            (void)dependsOnCoreCoder;
            uint8_t extensionFlag = (ASC & 0x01);
            (void)extensionFlag;

            if(frameLengthFlag == 0) AUDIO_INFO("AAC FrameLength: 1024 bytes");
            if(frameLengthFlag == 1) AUDIO_INFO("AAC FrameLength: 960 bytes");
        }
        if(specialIndexOf(data, "mp4a", len) > 0) {
            int offset = specialIndexOf(data, "mp4a", len);
            int channel = bigEndian(data + offset + 20, 2); // audio parameter must be set before starting
            int bps = bigEndian(data + offset + 22, 2);     // the aac decoder. There are RAW blocks only in m4a
            int srate = bigEndian(data + offset + 26, 4);   //
            setBitsPerSample(bps);
            setChannels(channel);
            setSampleRate(srate);
            setBitrate(bps * channel * srate);
            AUDIO_INFO("ch; %i, bps: %i, sr: %i", channel, bps, srate);
            if(audioDataPos && getDatamode() == AUDIO_LOCALFILE) {
                m_controlCounter = M4A_AMRDY;
                setFilePos(audioDataPos);
                return 0;
            }
        }
        m_controlCounter = M4A_MOOV;
        return 0;
    }
    // - - - - - - - - - - - - - - - - - - - - - - - - - - - - - - - - - - - - - - - -
    if(m_controlCounter == M4A_ILST) { // ilst
        const char info[12][6] = {"nam\0", "ART\0", "alb\0", "too\0", "cmt\0", "wrt\0", "tmpo\0", "trkn\0", "day\0", "cpil\0", "aART\0", "gen\0"};
        int        offset = 0;
        // If it's a local file, the metadata has already been read, even if it comes after the audio block.
        // In the event that they are in front of the audio block in a web stream, read them now
        if(!m_f_m4aID3dataAreRead) {
            for(int i = 0; i < 12; i++) {
                offset = specialIndexOf(data, info[i], len, true); // seek info[] with '\0'
                if(offset > 0) {
                    offset += 19;
                    if(*(data + offset) == 0) offset++;
                    char   value[256] = {0};
                    size_t tmp = strlen((const char*)data + offset);
                    if(tmp > 254) tmp = 254;
                    memcpy(value, (data + offset), tmp);
                    value[tmp] = '\0';
                    m_chbuf[0] = '\0';
                    if(i == 0) sprintf(m_chbuf, "Title: %s", value);
                    if(i == 1) sprintf(m_chbuf, "Artist: %s", value);
                    if(i == 2) sprintf(m_chbuf, "Album: %s", value);
                    if(i == 3) sprintf(m_chbuf, "Encoder: %s", value);
                    if(i == 4) sprintf(m_chbuf, "Comment: %s", value);
                    if(i == 5) sprintf(m_chbuf, "Composer: %s", value);
                    if(i == 6) sprintf(m_chbuf, "BPM: %s", value);
                    if(i == 7) sprintf(m_chbuf, "Track Number: %s", value);
                    if(i == 8) sprintf(m_chbuf, "Year: %s", value);
                    if(i == 9) sprintf(m_chbuf, "Compile: %s", value);
                    if(i == 10) sprintf(m_chbuf, "Album Artist: %s", value);
                    if(i == 11) sprintf(m_chbuf, "Types of: %s", value);
                    if(m_chbuf[0] != 0) {
                        if(audio_id3data) audio_id3data(m_chbuf);
                    }
                }
            }
        }
        offset = specialIndexOf(data, "covr", len);
        if(offset > 0){
            picLen = bigEndian(data + offset + 4, 4) - 4;
            picPos = headerSize + offset + 12;
        }
        m_controlCounter = M4A_MOOV;
        return 0;
    }
    // - - - - - - - - - - - - - - - - - - - - - - - - - - - - - - - - - - - - - - - -
    if(m_controlCounter == M4A_MDAT) {            // mdat
        m_audioDataSize = bigEndian(data, 4) - 8; // length of this atom - strlen(M4A_MDAT)
        AUDIO_INFO("Audio-Length: %u", m_audioDataSize);
        retvalue = 8;
        headerSize += 8;
        m_controlCounter = M4A_AMRDY; // last step before starting the audio
        return 0;
    }

    if(m_controlCounter == M4A_AMRDY) { // almost ready
        m_audioDataStart = headerSize;
        //        m_contentlength = headerSize + m_audioDataSize; // after this mdat atom there may be other atoms
        if(getDatamode() == AUDIO_LOCALFILE) { AUDIO_INFO("Content-Length: %lu", (long unsigned int)m_contentlength); }

        if(picLen) {
            size_t pos = audiofile.position();
            audio_id3image(audiofile, picPos, picLen);
            audiofile.seek(pos); // the filepointer could have been changed by the user, set it back
        }

        m_controlCounter = M4A_OKAY; // that's all
        return 0;
    }
    // this section should never be reached
    log_e("error");
    return 0;
}
//------------------------------------------------------------------------------------------------------------------------------------------------------------------------------------------------------
size_t Audio::process_m3u8_ID3_Header(uint8_t* packet) {
    uint8_t  ID3version;
    size_t   id3Size;
    bool     m_f_unsync = false, m_f_exthdr = false;
    uint64_t current_timestamp = 0;

    (void)m_f_unsync;        // suppress -Wunused-variable
    (void)current_timestamp; // suppress -Wunused-variable

    if(specialIndexOf(packet, "ID3", 4) != 0) { // ID3 not found
        if(m_f_Log) log_i("m3u8 file has no mp3 tag");
        return 0; // error, no ID3 signature found
    }
    ID3version = *(packet + 3);
    switch(ID3version) {
        case 2:
            m_f_unsync = (*(packet + 5) & 0x80);
            m_f_exthdr = false;
            break;
        case 3:
        case 4:
            m_f_unsync = (*(packet + 5) & 0x80); // bit7
            m_f_exthdr = (*(packet + 5) & 0x40); // bit6 extended header
            break;
    };
    id3Size = bigEndian(&packet[6], 4, 7); //  ID3v2 size  4 * %0xxxxxxx (shift left seven times!!)
    id3Size += 10;
    if(m_f_Log) log_i("ID3 framesSize: %i", id3Size);
    if(m_f_Log) log_i("ID3 version: 2.%i", ID3version);

    if(m_f_exthdr) {
        log_e("ID3 extended header in m3u8 files not supported");
        return 0;
    }
    if(m_f_Log) log_i("ID3 normal frames");

    if(specialIndexOf(&packet[10], "PRIV", 5) != 0) { // tag PRIV not found
        log_e("tag PRIV in m3u8 Id3 Header not found");
        return 0;
    }
    // if tag PRIV exists assume content is "com.apple.streaming.transportStreamTimestamp"
    // a time stamp is expected in the header.

    current_timestamp = (double)bigEndian(&packet[69], 4) / 90000; // seconds

    return id3Size;
}
//------------------------------------------------------------------------------------------------------------------------------------------------------------------------------------------------------
uint32_t Audio::stopSong() {
    uint32_t pos = 0;
    if(m_f_running) {
        m_f_running = false;
        if(getDatamode() == AUDIO_LOCALFILE) {
            m_streamType = ST_NONE;
            pos = getFilePos() - inBufferFilled();
        }
        if(_client->connected()) _client->stop();
    }
    if(audiofile) {
        // added this before putting 'm_f_localfile = false' in stopSong(); shoulf never occur....
        AUDIO_INFO("Closing audio file \"%s\"", audiofile.name());
        audiofile.close();
    }
    memset(m_outBuff, 0, m_outbuffSize); // Clear OutputBuffer
    memset(m_filterBuff, 0, sizeof(m_filterBuff)); // Clear FilterBuffer
    m_validSamples = 0;
    m_audioCurrentTime = 0;
    m_audioFileDuration = 0;
    m_codec = CODEC_NONE;
    return pos;
}
//------------------------------------------------------------------------------------------------------------------------------------------------------------------------------------------------------
bool Audio::pauseResume() {
    xSemaphoreTake(mutex_audio, portMAX_DELAY);
    bool retVal = false;
    if(getDatamode() == AUDIO_LOCALFILE || m_streamType == ST_WEBSTREAM || m_streamType == ST_WEBFILE) {
        m_f_running = !m_f_running;
        retVal = true;
        if(!m_f_running) {
            memset(m_outBuff, 0, m_outbuffSize); // Clear OutputBuffer
            m_validSamples = 0;
        }
    }
    xSemaphoreGive(mutex_audio);
    return retVal;
}
//------------------------------------------------------------------------------------------------------------------------------------------------------------------------------------------------------
void Audio::playChunk() {

    int16_t sample[2];

    auto pc = [&](int16_t* s16) { // lambda, inner function
        if(playSample(s16)) {
            m_validSamples--;
            m_curSample++;
            return true;
        }
        return false;
    };

    // If we've got data, try and pump it out..
    while(m_validSamples) {
        if(getBitsPerSample() == 8) {
            if(getChannels() == 1) {
                uint8_t x = m_outBuff[m_curSample] & 0x00FF;
                uint8_t y = (m_outBuff[m_curSample] & 0xFF00) >> 8;
                sample[RIGHTCHANNEL] = x;
                sample[LEFTCHANNEL] = x;
                if(!pc(sample)) { /* break */; } // playSample in lambda
                sample[RIGHTCHANNEL] = y;
                sample[LEFTCHANNEL] = y;
                if(!pc(sample)) { /* break */; } // playSample in lambda
            }
            if(getChannels() == 2) {
                uint8_t x = m_outBuff[m_curSample] & 0x00FF;
                uint8_t y = (m_outBuff[m_curSample] & 0xFF00) >> 8;
                if(!m_f_forceMono) { // stereo mode
                    sample[RIGHTCHANNEL] = x;
                    sample[LEFTCHANNEL] = y;
                }
                else { // force mono
                    uint8_t xy = (x + y) / 2;
                    sample[RIGHTCHANNEL] = xy;
                    sample[LEFTCHANNEL] = xy;
                }
                if(!pc(sample)) { /* break */; } // playSample in lambda
            }
        }

        if(getBitsPerSample() == 16) {
            if(getChannels() == 1) {
                sample[RIGHTCHANNEL] = m_outBuff[m_curSample];
                sample[LEFTCHANNEL] = m_outBuff[m_curSample];
            }
            if(getChannels() == 2) {
                if(!m_f_forceMono) { // stereo mode
                    sample[RIGHTCHANNEL] = m_outBuff[m_curSample * 2];
                    sample[LEFTCHANNEL] = m_outBuff[m_curSample * 2 + 1];
                }
                else { // mono mode, #100
                    int16_t xy = (m_outBuff[m_curSample * 2] + m_outBuff[m_curSample * 2 + 1]) / 2;
                    sample[RIGHTCHANNEL] = xy;
                    sample[LEFTCHANNEL] = xy;
                }
            }
        }
        if(!pc(sample)) { break; } // playSample in lambda OMT: do not comment out!
    }
}
//------------------------------------------------------------------------------------------------------------------------------------------------------------------------------------------------------
void Audio::loop() {
    if(!m_f_running) return;

    xSemaphoreTake(mutex_audio, portMAX_DELAY);

    if(m_playlistFormat != FORMAT_M3U8) { // normal process
        switch(getDatamode()) {
            case AUDIO_LOCALFILE: processLocalFile(); break;
            case HTTP_RESPONSE_HEADER: parseHttpResponseHeader(); break;
            case AUDIO_PLAYLISTINIT: readPlayListData(); break;
            case AUDIO_PLAYLISTDATA:
                if(m_playlistFormat == FORMAT_M3U) connecttohost(parsePlaylist_M3U());
                if(m_playlistFormat == FORMAT_PLS) connecttohost(parsePlaylist_PLS());
                if(m_playlistFormat == FORMAT_ASX) connecttohost(parsePlaylist_ASX());
                break;
            case AUDIO_DATA:
                if(m_streamType == ST_WEBSTREAM) processWebStream();
                if(m_streamType == ST_WEBFILE) processWebFile();
                break;
        }
    }
    else { // m3u8 datastream only
        const char* host;

        switch(getDatamode()) {
            case HTTP_RESPONSE_HEADER:
                if(!parseHttpResponseHeader()) {
                    if(m_f_timeout) connecttohost(m_lastHost);
                }
                break;
            case AUDIO_PLAYLISTINIT: readPlayListData(); break;
            case AUDIO_PLAYLISTDATA:
                host = parsePlaylist_M3U8();
                if(host) { // host contains the next playlist URL
                    httpPrint(host);
                    setDatamode(HTTP_RESPONSE_HEADER);
                }
                else { // host == NULL means connect to m3u8 URL
                    if(host) httpPrint(m_lastM3U8host);
                    else httpPrint(m_lastHost);        // if url has no first redirection
                    setDatamode(HTTP_RESPONSE_HEADER); // we have a new playlist now
                }

                break;
            case AUDIO_DATA:
                if(m_f_ts) { processWebStreamTS(); } // aac or aacp with ts packets
                else { processWebStreamHLS(); }      // aac or aacp normal stream

                if(m_f_continue) { // at this point m_f_continue is true, means processWebStream() needs more data
                    setDatamode(AUDIO_PLAYLISTDATA);
                    m_f_continue = false;
                }
                break;
        }
    }
    xSemaphoreGive(mutex_audio);
}
//------------------------------------------------------------------------------------------------------------------------------------------------------------------------------------------------------
bool Audio::readPlayListData() {
    if(getDatamode() != AUDIO_PLAYLISTINIT) return false;
    if(_client->available() == 0) return false;

    uint32_t chunksize = 0;
    uint8_t  readedBytes = 0;
    if(m_f_chunked) chunksize = chunkedDataTransfer(&readedBytes);

    // reads the content of the playlist and stores it in the vector m_contentlength
    // m_contentlength is a table of pointers to the lines
    char     pl[512] = {0}; // playlistLine
    uint32_t ctl = 0;
    int      lines = 0;
    // delete all memory in m_playlistContent
    if(m_playlistFormat == FORMAT_M3U8 && !psramFound()) { log_e("m3u8 playlists requires PSRAM enabled!"); }
    vector_clear_and_shrink(m_playlistContent);
    while(true) { // outer while

        uint32_t ctime = millis();
        uint32_t timeout = 2000; // ms

        while(true) { // inner while
            uint16_t pos = 0;
            while(_client->available()) { // super inner while :-))
                pl[pos] = _client->read();
                ctl++;
                if(pl[pos] == '\n') {
                    pl[pos] = '\0';
                    pos++;
                    break;
                }
                //    if(pl[pos] == '&' ) {pl[pos] = '\0'; pos++; break;}
                if(pl[pos] == '\r') {
                    pl[pos] = '\0';
                    pos++;
                    continue;
                    ;
                }
                pos++;
                if(pos == 510) {
                    pos--;
                    continue;
                }
                if(pos == 509) { pl[pos] = '\0'; }
                if(ctl == chunksize) {
                    pl[pos] = '\0';
                    break;
                }
                if(ctl == m_contentlength) {
                    pl[pos] = '\0';
                    break;
                }
            }
            if(ctl == chunksize) break;
            if(ctl == m_contentlength) break;
            if(pos) {
                pl[pos] = '\0';
                break;
            }

            if(ctime + timeout < millis()) {
                log_e("timeout");
                for(int i = 0; i < m_playlistContent.size(); i++) log_e("pl%i = %s", i, m_playlistContent[i]);
                goto exit;
            }
        } // inner while

        if(startsWith(pl, "<!DOCTYPE")) {
            AUDIO_INFO("url is a webpage!");
            goto exit;
        }
        if(startsWith(pl, "<html")) {
            AUDIO_INFO("url is a webpage!");
            goto exit;
        }
        if(strlen(pl) > 0) m_playlistContent.push_back(x_strdup(pl));
        if(!m_f_psramFound && m_playlistContent.size() == 101) {
            AUDIO_INFO("the number of lines in playlist > 100, for bigger playlist use PSRAM!");
            break;
        }
        if(m_playlistContent.size() && m_playlistContent.size() % 1000 == 0) { AUDIO_INFO("current playlist line: %lu", (long unsigned)m_playlistContent.size()); }
        // termination conditions
        // 1. The http response header returns a value for contentLength -> read chars until contentLength is reached
        // 2. no contentLength, but Transfer-Encoding:chunked -> compute chunksize and read until chunksize is reached
        // 3. no chunksize and no contentlengt, but Connection: close -> read all available chars
        if(ctl == m_contentlength) {
            while(_client->available()) _client->read();
            break;
        } // read '\n\n' if exists
        if(ctl == chunksize) {
            while(_client->available()) _client->read();
            break;
        }
        if(!_client->connected() && _client->available() == 0) break;

    } // outer while
    lines = m_playlistContent.size();
    for(int i = 0; i < lines; i++) { // print all string in first vector of 'arr'
        if(m_f_Log) log_i("pl=%i \"%s\"", i, m_playlistContent[i]);
    }
    setDatamode(AUDIO_PLAYLISTDATA);
    return true;

exit:
    vector_clear_and_shrink(m_playlistContent);
    m_f_running = false;
    setDatamode(AUDIO_NONE);
    return false;
}
//-------------------------------------------------------------------------------------------------------------------------------------------------------------------------------------------------------
const char* Audio::parsePlaylist_M3U() {
    uint8_t lines = m_playlistContent.size();
    int     pos = 0;
    char*   host = nullptr;

    for(int i = 0; i < lines; i++) {
        if(indexOf(m_playlistContent[i], "#EXTINF:") >= 0) { // Info?
            pos = indexOf(m_playlistContent[i], ",");        // Comma in this line?
            if(pos > 0) {
                // Show artist and title if present in metadata
                AUDIO_INFO(m_playlistContent[i] + pos + 1);
            }
            continue;
        }
        if(startsWith(m_playlistContent[i], "#")) { // Commentline?
            continue;
        }

        pos = indexOf(m_playlistContent[i], "http://:@", 0); // ":@"??  remove that!
        if(pos >= 0) {
            AUDIO_INFO("Entry in playlist found: %s", (m_playlistContent[i] + pos + 9));
            host = m_playlistContent[i] + pos + 9;
            break;
        }
        // AUDIO_INFO("Entry in playlist found: %s", pl);
        pos = indexOf(m_playlistContent[i], "http", 0); // Search for "http"
        if(pos >= 0) {                                  // Does URL contain "http://"?
                                                        //    log_e("%s pos=%i", m_playlistContent[i], pos);
            host = m_playlistContent[i] + pos;          // Yes, set new host
            break;
        }
    }
    //    vector_clear_and_shrink(m_playlistContent);
    return host;
}
//-------------------------------------------------------------------------------------------------------------------------------------------------------------------------------------------------------
const char* Audio::parsePlaylist_PLS() {
    uint8_t lines = m_playlistContent.size();
    int     pos = 0;
    char*   host = nullptr;

    for(int i = 0; i < lines; i++) {
        if(i == 0) {
            if(strlen(m_playlistContent[0]) == 0) goto exit;      // empty line
            if(strcmp(m_playlistContent[0], "[playlist]") != 0) { // first entry in valid pls
                setDatamode(HTTP_RESPONSE_HEADER);                // pls is not valid
                AUDIO_INFO("pls is not valid, switch to HTTP_RESPONSE_HEADER");
                goto exit;
            }
            continue;
        }
        if(startsWith(m_playlistContent[i], "File1")) {
            if(host) continue;                              // we have already a url
            pos = indexOf(m_playlistContent[i], "http", 0); // File1=http://streamplus30.leonex.de:14840/;
            if(pos >= 0) {                                  // yes, URL contains "http"?
                host = m_playlistContent[i] + pos;          // Now we have an URL for a stream in host.
            }
            continue;
        }
        if(startsWith(m_playlistContent[i], "Title1")) { // Title1=Antenne Tirol
            const char* plsStationName = (m_playlistContent[i] + 7);
            if(audio_showstation) audio_showstation(plsStationName);
            AUDIO_INFO("StationName: \"%s\"", plsStationName);
            continue;
        }
        if(startsWith(m_playlistContent[i], "Length1")) { continue; }
        if(indexOf(m_playlistContent[i], "Invalid username") >= 0) { // Unable to access account:
            goto exit;                                               // Invalid username or password
        }
    }
    return host;

exit:
    m_f_running = false;
    stopSong();
    vector_clear_and_shrink(m_playlistContent);
    setDatamode(AUDIO_NONE);
    return nullptr;
}
//-------------------------------------------------------------------------------------------------------------------------------------------------------------------------------------------------------
const char* Audio::parsePlaylist_ASX() { // Advanced Stream Redirector
    uint8_t lines = m_playlistContent.size();
    bool    f_entry = false;
    int     pos = 0;
    char*   host = nullptr;

    for(int i = 0; i < lines; i++) {
        int p1 = indexOf(m_playlistContent[i], "<", 0);
        int p2 = indexOf(m_playlistContent[i], ">", 1);
        if(p1 >= 0 && p2 > p1) { // #196 set all between "< ...> to lowercase
            for(uint8_t j = p1; j < p2; j++) { m_playlistContent[i][j] = toLowerCase(m_playlistContent[i][j]); }
        }
        if(indexOf(m_playlistContent[i], "<entry>") >= 0) f_entry = true; // found entry tag (returns -1 if not found)
        if(f_entry) {
            if(indexOf(m_playlistContent[i], "ref href") > 0) { //  <ref href="http://87.98.217.63:24112/stream" />
                pos = indexOf(m_playlistContent[i], "http", 0);
                if(pos > 0) {
                    host = (m_playlistContent[i] + pos); // http://87.98.217.63:24112/stream" />
                    int pos1 = indexOf(host, "\"", 0);   // http://87.98.217.63:24112/stream
                    if(pos1 > 0) host[pos1] = '\0';      // Now we have an URL for a stream in host.
                }
            }
        }
        pos = indexOf(m_playlistContent[i], "<title>", 0);
        if(pos >= 0) {
            char* plsStationName = (m_playlistContent[i] + pos + 7); // remove <Title>
            pos = indexOf(plsStationName, "</", 0);
            if(pos >= 0) {
                *(plsStationName + pos) = 0; // remove </Title>
            }
            if(audio_showstation) audio_showstation(plsStationName);
            AUDIO_INFO("StationName: \"%s\"", plsStationName);
        }

        if(indexOf(m_playlistContent[i], "http") == 0 && !f_entry) { // url only in asx
            host = m_playlistContent[i];
        }
    }
    return host;
}
//-------------------------------------------------------------------------------------------------------------------------------------------------------------------------------------------------------
const char* Audio::parsePlaylist_M3U8() {

    // example: audio chunks
    // #EXTM3U
    // #EXT-X-TARGETDURATION:10
    // #EXT-X-MEDIA-SEQUENCE:163374040
    // #EXT-X-DISCONTINUITY
    // #EXTINF:10,title="text=\"Spot Block End\" amgTrackId=\"9876543\"",artist=" ",url="length=\"00:00:00\""
    // http://n3fa-e2.revma.ihrhls.com/zc7729/63_sdtszizjcjbz02/main/163374038.aac
    // #EXTINF:10,title="text=\"Spot Block End\" amgTrackId=\"9876543\"",artist=" ",url="length=\"00:00:00\""
    // http://n3fa-e2.revma.ihrhls.com/zc7729/63_sdtszizjcjbz02/main/163374039.aac

    static uint64_t xMedSeq = 0;
    static boolean  f_mediaSeq_found = false;
    boolean         f_EXTINF_found = false;
    char            llasc[21]; // uint64_t max = 18,446,744,073,709,551,615  thats 20 chars + \0
    if(m_f_firstM3U8call) {
        m_f_firstM3U8call = false;
        xMedSeq = 0;
        f_mediaSeq_found = false;
    }

    uint8_t     lines = m_playlistContent.size();
    bool        f_begin = false;
    const char* ret;
    if(lines) {
        for(uint16_t i = 0; i < lines; i++) {
            if(strlen(m_playlistContent[i]) == 0) continue; // empty line
            if(startsWith(m_playlistContent[i], "#EXTM3U")) {
                f_begin = true;
                continue;
            } // what we expected
            if(!f_begin) continue;

            if(startsWith(m_playlistContent[i], "#EXT-X-STREAM-INF:")) {
                uint8_t codec = CODEC_NONE;
                ret = m3u8redirection(&codec);
                if(ret) {
                    m_codec = codec; // can be AAC or MP3
                    return ret;
                }
            }
            if(m_codec == CODEC_NONE) m_codec = CODEC_AAC; // if we have no redirection

            // "#EXT-X-DISCONTINUITY-SEQUENCE: // not used, 0: seek for continuity numbers, is sometimes not set
            // "#EXT-X-MEDIA-SEQUENCE:"        // not used, is unreliable
            if(startsWith(m_playlistContent[i], "#EXT-X-VERSION:")) continue;
            if(startsWith(m_playlistContent[i], "#EXT-X-ALLOW-CACHE:")) continue;
            if(startsWith(m_playlistContent[i], "##")) continue;
            if(startsWith(m_playlistContent[i], "#EXT-X-INDEPENDENT-SEGMENTS")) continue;
            if(startsWith(m_playlistContent[i], "#EXT-X-PROGRAM-DATE-TIME:")) continue;

            if(!f_mediaSeq_found) {
                xMedSeq = m3u8_findMediaSeqInURL();
                if(xMedSeq == UINT64_MAX) {
                    log_e("X MEDIA SEQUENCE NUMBER not found");
                    stopSong();
                    return NULL;
                }
                if(xMedSeq > 0) f_mediaSeq_found = true;
                if(xMedSeq == 0) { // mo mediaSeqNr but min 3 times #EXTINF found
                    ;
                }
            }

            if(startsWith(m_playlistContent[i], "#EXTINF")) {
                f_EXTINF_found = true;
                if(STfromEXTINF(m_playlistContent[i])) { showstreamtitle(m_chbuf); }
                i++;
                if(startsWith(m_playlistContent[i], "#")) i++;   // #MY-USER-CHUNK-DATA-1:ON-TEXT-DATA="20....
                if(i == lines) continue; // and exit for()

                char* tmp = nullptr;
                if(!startsWith(m_playlistContent[i], "http")) {

                        //  playlist:   http://station.com/aaa/bbb/xxx.m3u8
                        //  chunklist:  http://station.com/aaa/bbb/ddd.aac
                        //  result:     http://station.com/aaa/bbb/ddd.aac

                    if(m_lastM3U8host != 0) {
                        tmp = (char*)malloc(strlen(m_lastM3U8host) + strlen(m_playlistContent[i]) + 1);
                        strcpy(tmp, m_lastM3U8host);
                    }
                    else {
                        tmp = (char*)malloc(strlen(m_lastHost) + strlen(m_playlistContent[i]) + 1);
                        strcpy(tmp, m_lastHost);
                    }


                    if(m_playlistContent[i][0] != '/'){

                        //  playlist:   http://station.com/aaa/bbb/xxx.m3u8  // tmp
                        //  chunklist:  ddd.aac                              // m_playlistContent[i]
                        //  result:     http://station.com/aaa/bbb/ddd.aac   // m_playlistContent[i]

                        int idx = lastIndexOf(tmp, "/");
                        tmp[idx  + 1] = '\0';
                        strcat(tmp, m_playlistContent[i]);
                    }
                    else{

                        //  playlist:   http://station.com/aaa/bbb/xxx.m3u8
                        //  chunklist:  /aaa/bbb/ddd.aac
                        //  result:     http://station.com/aaa/bbb/ddd.aac

                        int idx = indexOf(tmp, "/", 8);
                        tmp[idx] = '\0';
                        strcat(tmp, m_playlistContent[i]);
                    }
                }
                else { tmp = strdup(m_playlistContent[i]); }

                if(f_mediaSeq_found) {
                    lltoa(xMedSeq, llasc, 10);
                    if(indexOf(tmp, llasc) > 0) {
                        m_playlistURL.insert(m_playlistURL.begin(), strdup(tmp));
                        xMedSeq++;
                    }
                    else{
                        lltoa(xMedSeq + 1, llasc, 10);
                        if(indexOf(tmp, llasc) > 0) {
                            m_playlistURL.insert(m_playlistURL.begin(), strdup(tmp));
                            log_w("mediaseq %llu skipped", xMedSeq);
                            xMedSeq+= 2;
                        }
                    }
                }
                else { // without mediaSeqNr, with hash
                    uint32_t hash = simpleHash(tmp);
                    if(m_hashQueue.size() == 0) {
                        m_hashQueue.insert(m_hashQueue.begin(), hash);
                        m_playlistURL.insert(m_playlistURL.begin(), strdup(tmp));
                    }
                    else {
                        bool known = false;
                        for(int i = 0; i < m_hashQueue.size(); i++) {
                            if(hash == m_hashQueue[i]) {
                                if(m_f_Log) log_i("file already known %s", tmp);
                                known = true;
                            }
                        }
                        if(!known) {
                            m_hashQueue.insert(m_hashQueue.begin(), hash);
                            m_playlistURL.insert(m_playlistURL.begin(), strdup(tmp));
                        }
                    }
                    if(m_hashQueue.size() > 20) m_hashQueue.pop_back();
                }

                if(tmp) {free(tmp); tmp = NULL;}

                continue;
            }
        }
        vector_clear_and_shrink(m_playlistContent); // clear after reading everything, m_playlistContent.size is now 0
    }

    if(m_playlistURL.size() > 0) {
        if(m_playlistBuff) {free(m_playlistBuff); m_playlistBuff = NULL;}

        if(m_playlistURL[m_playlistURL.size() - 1]) {
            m_playlistBuff = strdup(m_playlistURL[m_playlistURL.size() - 1]);
            free(m_playlistURL[m_playlistURL.size() - 1]);
            m_playlistURL[m_playlistURL.size() - 1] = NULL;
            m_playlistURL.pop_back();
            m_playlistURL.shrink_to_fit();
        }
        if(m_f_Log) log_i("now playing %s", m_playlistBuff);
        if(endsWith(m_playlistBuff, "ts")) m_f_ts = true;
        if(indexOf(m_playlistBuff, ".ts?") > 0) m_f_ts = true;
        return m_playlistBuff;
    }
    else {
        if(f_EXTINF_found) {
            if(f_mediaSeq_found) {
                if(m_playlistContent.size() == 0) return NULL;
                uint64_t mediaSeq = m3u8_findMediaSeqInURL();
                if(xMedSeq == 0 || xMedSeq == UINT64_MAX) {
                    log_e("xMediaSequence not found");
                    connecttohost(m_lastHost);
                }
                if(mediaSeq < xMedSeq) {
                    uint64_t diff = xMedSeq - mediaSeq;
                    if(diff < 10) { ; }
                    else {
                        if(m_playlistContent.size() > 0) {
                            for(int j = 0; j < lines; j++) {
                                if(m_f_Log) log_i("lines %i, %s", lines, m_playlistContent[j]);
                            }
                        }
                        else { ; }

                        if(m_playlistURL.size() > 0) {
                            for(int j = 0; j < m_playlistURL.size(); j++) {
                                if(m_f_Log) log_i("m_playlistURL lines %i, %s", j, m_playlistURL[j]);
                            }
                        }
                        else { ; }

                        if(m_playlistURL.size() == 0) {
                            connecttohost(m_lastHost);
                        }
                    }
                }
                else {
                    if(mediaSeq != UINT64_MAX) { log_e("err, %u packets lost from %u, to %u", mediaSeq - xMedSeq, xMedSeq, mediaSeq); }
                    xMedSeq = mediaSeq;
                }
            } // f_medSeq_found
        }
    }
    playAudioData(); // avoid audio gap
    return NULL;
}
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
